blakhall/Kicad/3dmodels/power_dcdc/SY8088AAC.step

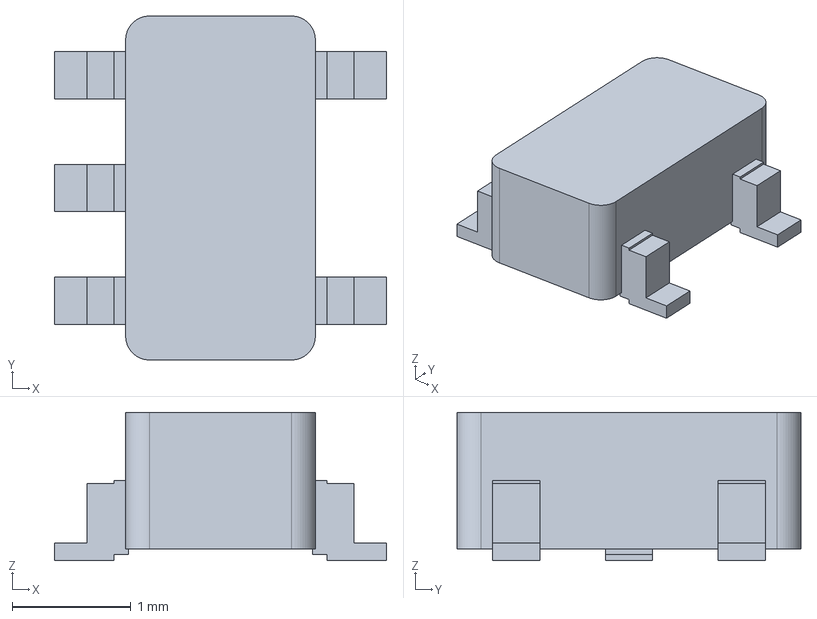
[picture p15: CAD file, 2026-08-23]
3dmodels/power_dcdc/SY8088AAC.step
2.80 x 2.90 x 1.25 mm
