blakhall/Kicad/3dmodels/so_gen/SOIC-6-Stretched_DWY_TI.step

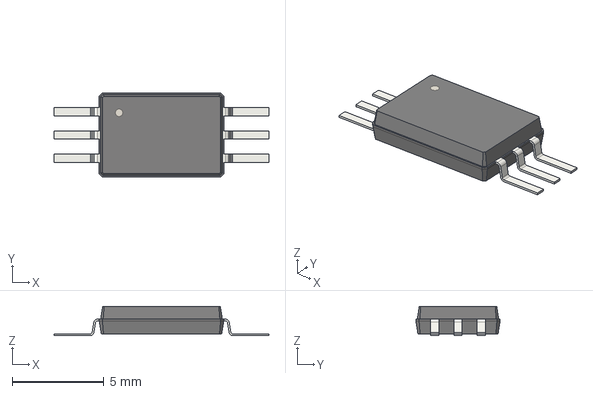
[picture p16: CAD file, 2026-08-02]
3dmodels/so_gen/SOIC-6-Stretched_DWY_TI.step
11.7 x 4.60 x 1.60 mm
