blakhall/Kicad/3dmodels/wpt_driver/SOIC-16_3.9x9.9mm_P1.27mm.step

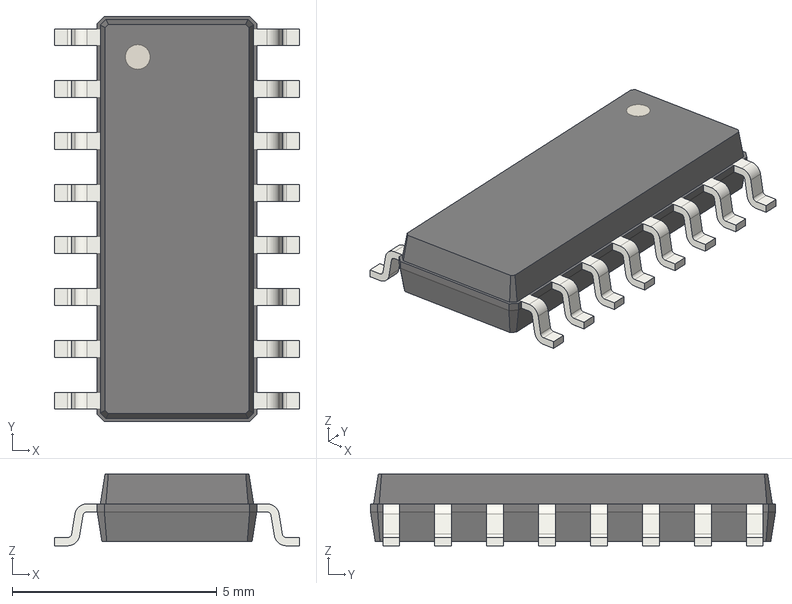
[picture p17: CAD file, 2026-09-19]
3dmodels/wpt_driver/SOIC-16_3.9x9.9mm_P1.27mm.step
6.00 x 9.90 x 1.75 mm
