blakhall/Kicad/3dmodels/wpt_magnetics/SCF29XV-200-2R0A011JV.step

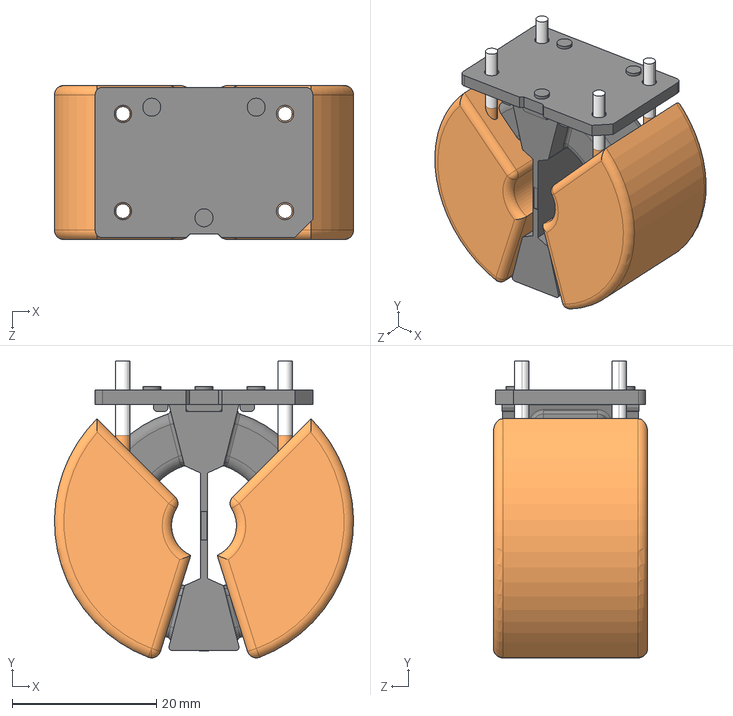
[picture p18: CAD file, 2026-09-19]
3dmodels/wpt_magnetics/SCF29XV-200-2R0A011JV.step
41.5 x 41.2 x 21.4 mm
