blakhall/Kicad/3dmodels/common/Celem_CSM_Nano.step

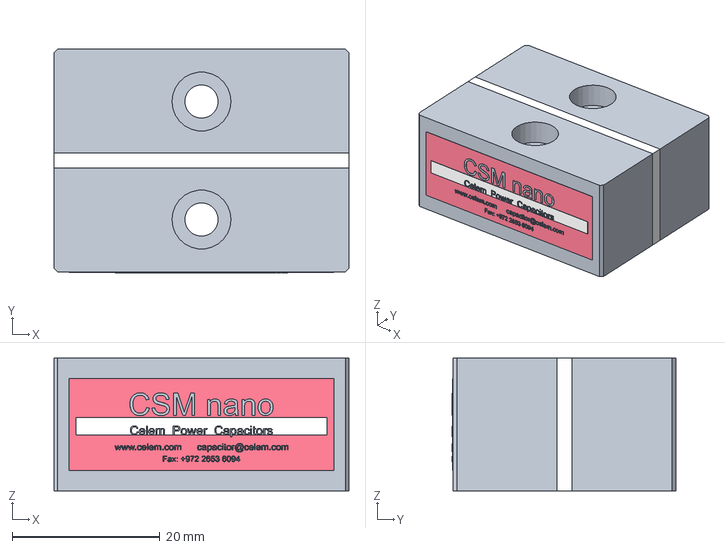
[picture p20: CAD file, 2026-09-17]
3dmodels/common/Celem_CSM_Nano.step
40.0 x 30.3 x 18.0 mm
