blakhall/Kicad/3dmodels/common/led/led-2012-orange.step

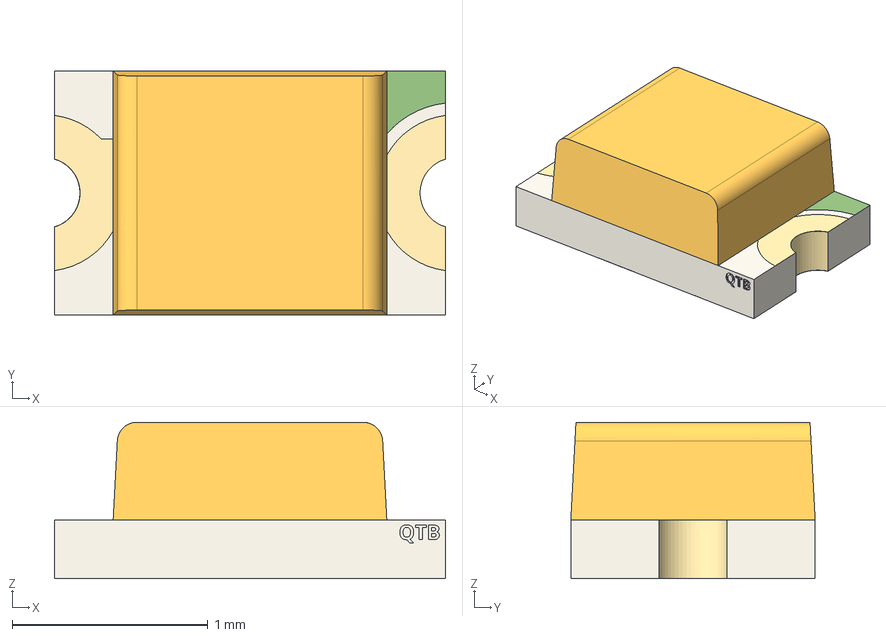
[picture p21: CAD file, 2025-10-02]
3dmodels/common/led/led-2012-orange.step
2.00 x 1.25 x 0.8 mm
Resin
Polarity Mark
Side Pad 1
Side Pad 2
Bottom Pad 2
Top Pad 2
Top Pad 1
Bottom Pad 1
Substrate
Bottom Pad - Mid
