blakhall/Kicad/3dmodels/common_gen/HVSON08_3X3_NXP.step

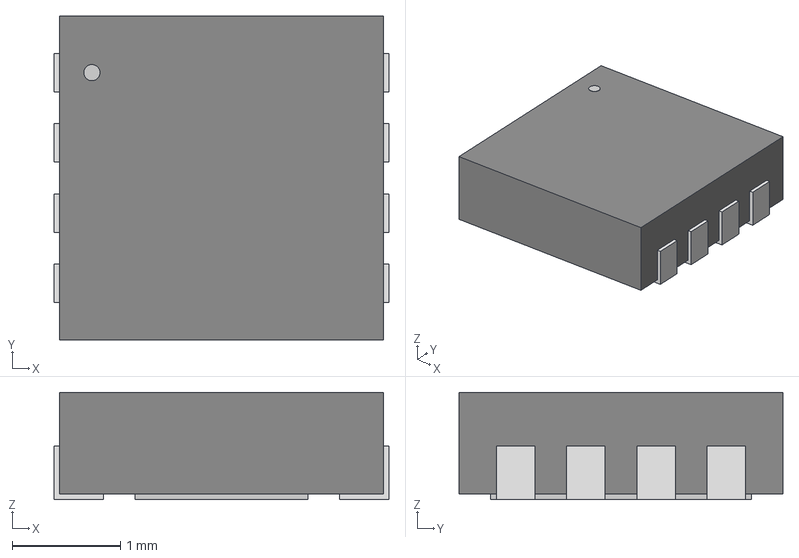
[picture p22: CAD file, 2026-08-17]
3dmodels/common_gen/HVSON08_3X3_NXP.step
3.10 x 3.00 x 0.993 mm
