blakhall/Kicad/3dmodels/connectors/FTR-110-51-L-D-06.step

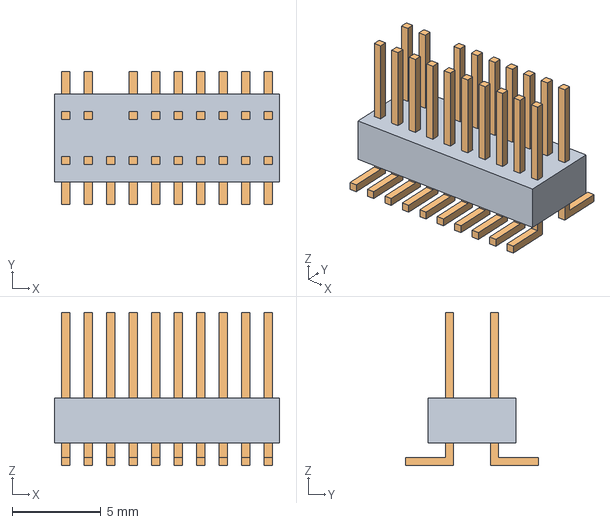
[picture p23: CAD file, 2026-09-19]
3dmodels/connectors/FTR-110-51-L-D-06.step
12.7 x 7.52 x 8.64 mm
