blakhall/Kicad/3dmodels/connectors/optic/HFBR-X41X.STEP

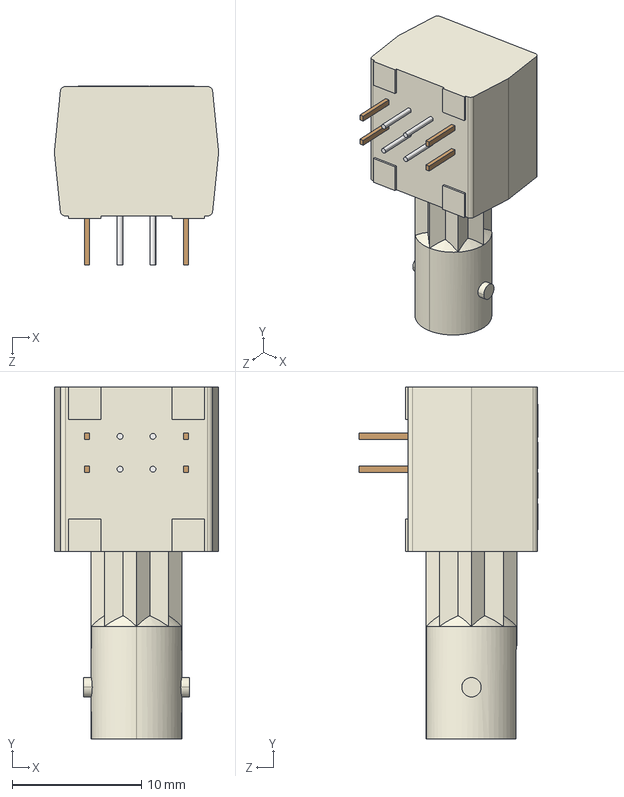
[picture p24: CAD file, 2025-12-01]
3dmodels/connectors/optic/HFBR-X41X.STEP
12.7 x 27.2 x 13.8 mm
HFBR-X41X Part1
HFBR-X41X Part2 x 4
HFBR-X41X Part3 x 4
HFBR-X41X Part4
