blakhall/Kicad/3dmodels/dsp_connectors/FTSH-122-03-L-DV.step

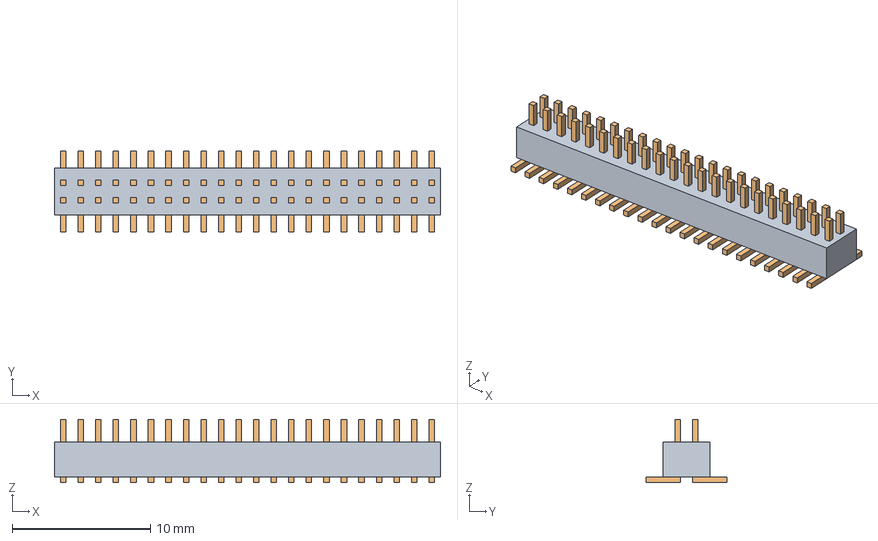
[picture p25: CAD file, 2026-09-19]
3dmodels/dsp_connectors/FTSH-122-03-L-DV.step
27.9 x 5.84 x 4.57 mm
