blakhall/Kicad/3dmodels/mcu_gen/IC_IS31CG5317-LQLS3_LQFP80.step

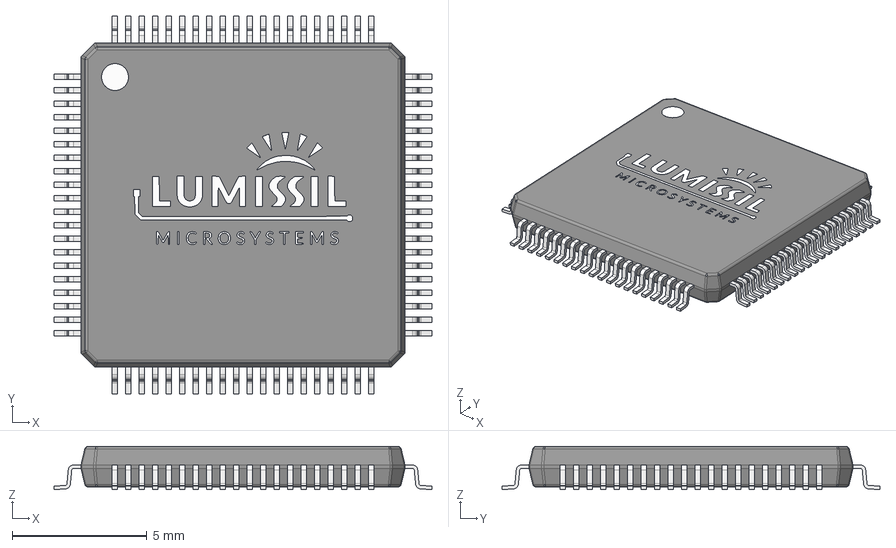
[picture p26: CAD file, 2026-07-20]
3dmodels/mcu_gen/IC_IS31CG5317-LQLS3_LQFP80.step
14.0 x 14.0 x 1.60 mm
Package
Leads
Mark
Logo
