blakhall/Kicad/3dmodels/power_gen/Celem_CSM_IPT.step

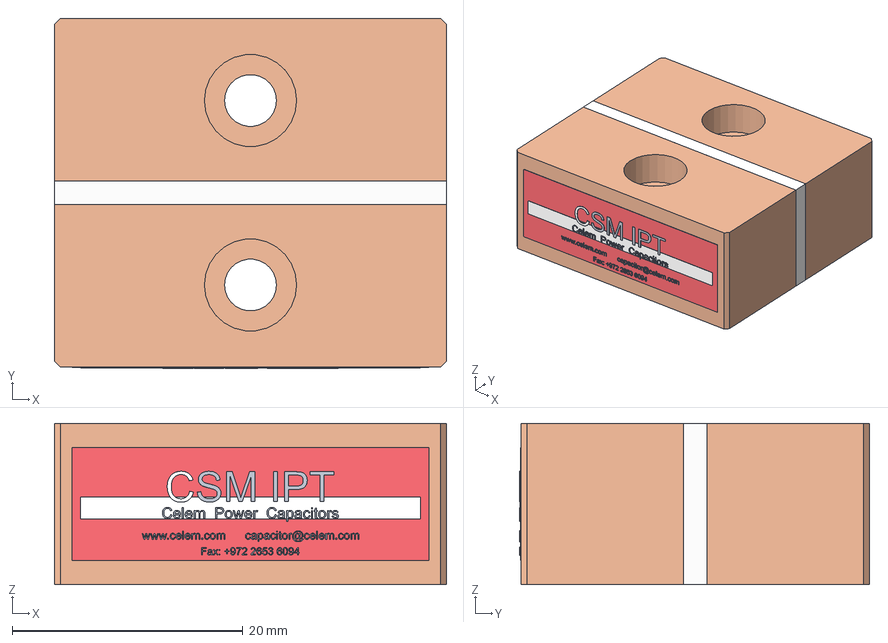
[picture p27: CAD file, 2026-09-17]
3dmodels/power_gen/Celem_CSM_IPT.step
34.0 x 30.3 x 14.0 mm
Copper_Electrode_Front
Copper_Electrode_Rear
Dielectric_Insulator
Celem_Red_Badge
Badge_White_Banner
Badge_Text_Markings
