blakhall/Kicad/3dmodels/so_gen/FC-BPGA-306_SOT2200-1_NXP.step

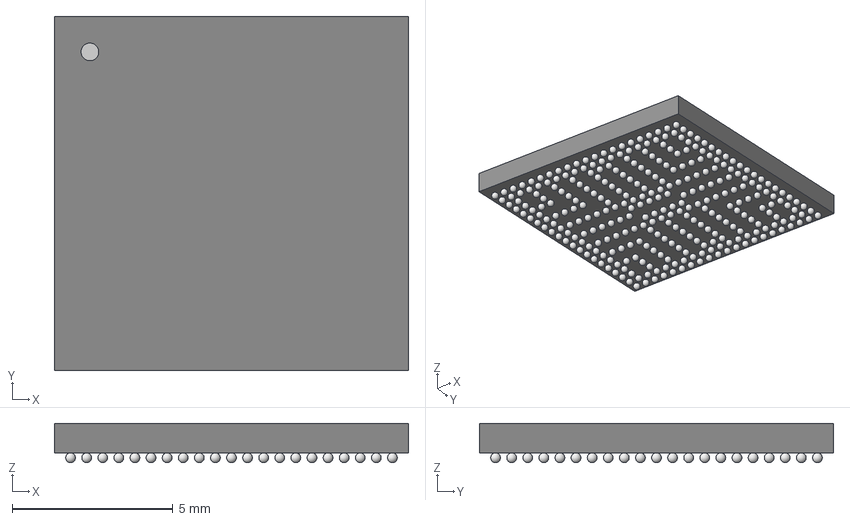
[picture p28: CAD file, 2026-03-11]
3dmodels/so_gen/FC-BPGA-306_SOT2200-1_NXP.step
11.0 x 11.0 x 1.22 mm
