blakhall/Kicad/3dmodels/wpt_driver/VSSOP-8_2.3x2mm_P0.5mm.step

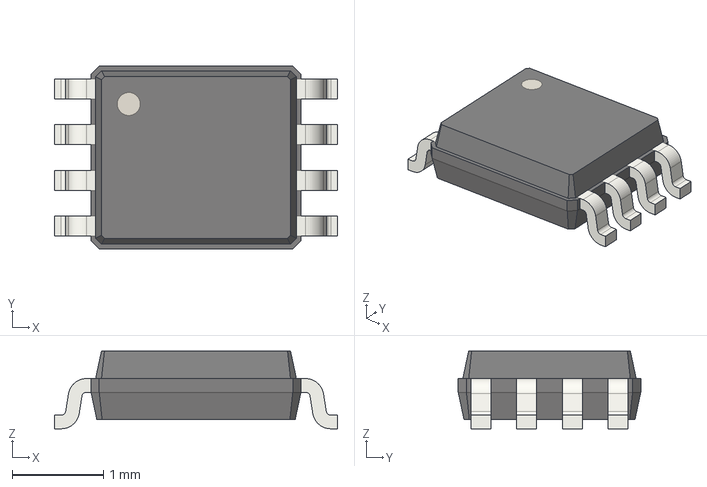
[picture p29: CAD file, 2026-09-19]
3dmodels/wpt_driver/VSSOP-8_2.3x2mm_P0.5mm.step
3.10 x 2.00 x 0.85 mm
