blakhall/Kicad/3dmodels/wpt_sensing/R_1206_3216Metric.step

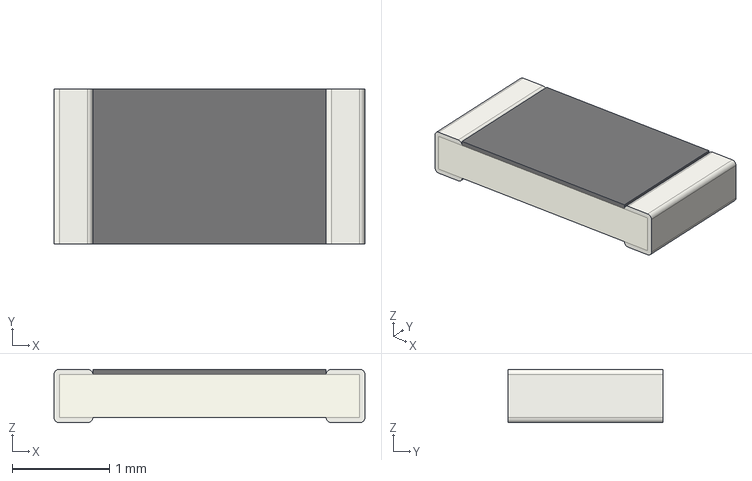
[picture p30: CAD file, 2026-09-19]
3dmodels/wpt_sensing/R_1206_3216Metric.step
3.20 x 1.60 x 0.55 mm
