blakhall/Kicad/3dmodels/common_gen/uQFN-6L_1.5x1.7mm_P0.5mm.step

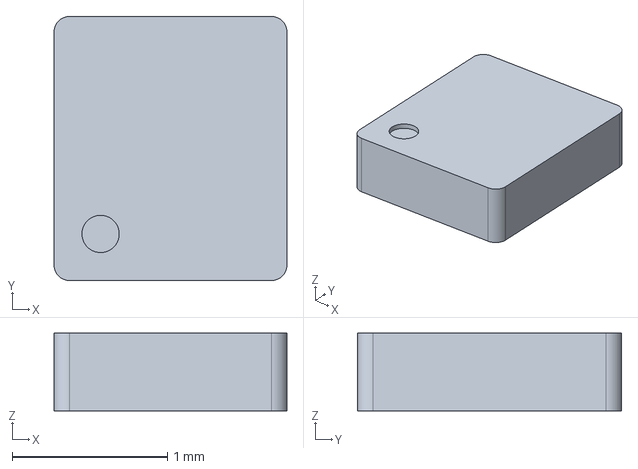
[picture p31: CAD file, 2026-08-17]
3dmodels/common_gen/uQFN-6L_1.5x1.7mm_P0.5mm.step
1.50 x 1.70 x 0.5 mm
