blakhall/Kicad/3dmodels/connectors/FTSH-104-03-L-DV.step

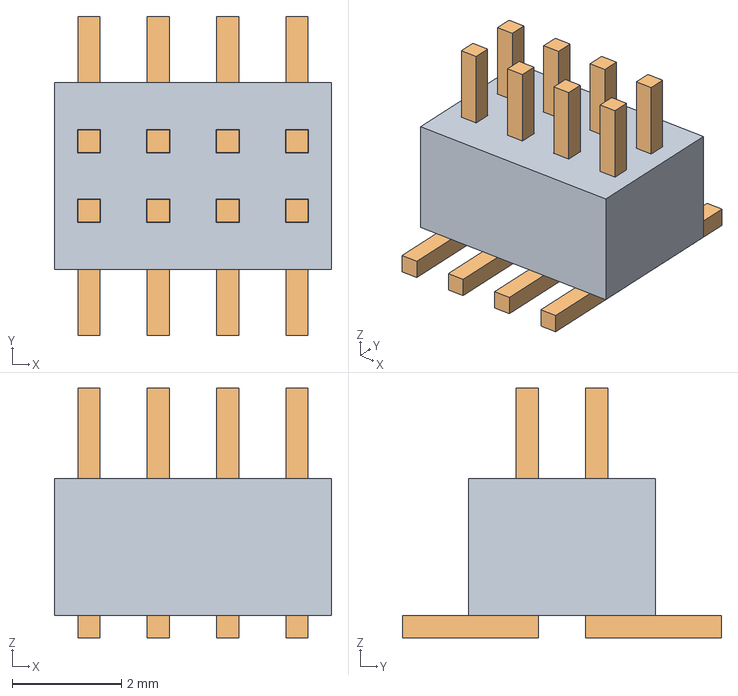
[picture p32: CAD file, 2026-09-19]
3dmodels/connectors/FTSH-104-03-L-DV.step
5.08 x 5.84 x 4.57 mm
