blakhall/Kicad/3dmodels/power_dcdc/SOIC-36W_7.5x12.8mm_P0.65mm_DWN_TI.step

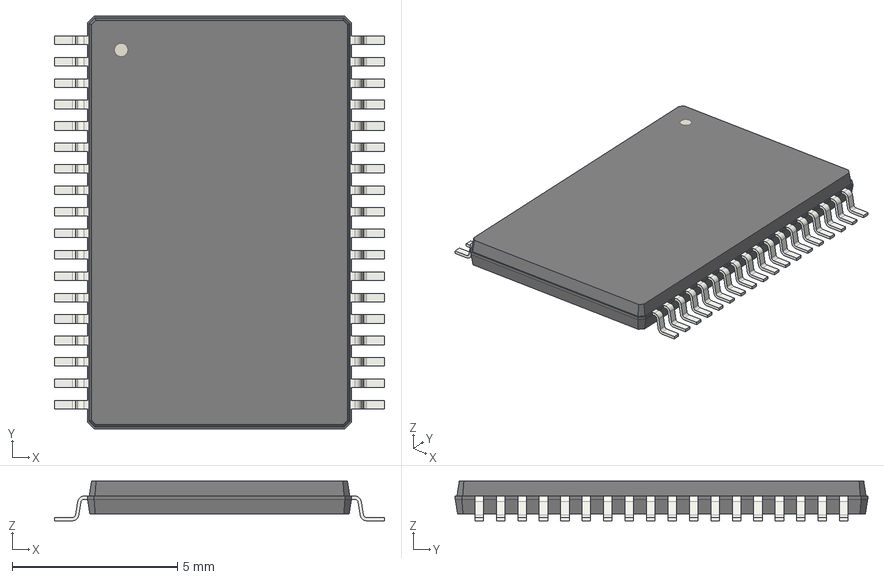
[picture p33: CAD file, 2026-08-02]
3dmodels/power_dcdc/SOIC-36W_7.5x12.8mm_P0.65mm_DWN_TI.step
10.0 x 12.5 x 1.20 mm
