blakhall/Kicad/3dmodels/so_gen/TQFP 128 0.4mm.stp

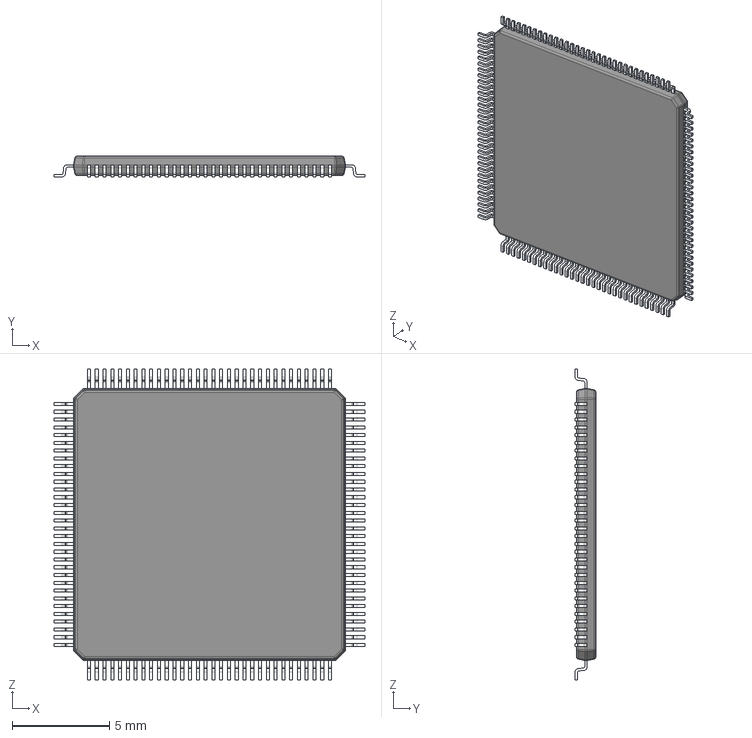
[picture p34: CAD file, 2025-09-22]
3dmodels/so_gen/TQFP 128 0.4mm.stp
16.0 x 1.07 x 16.0 mm
BODY_VJX128A
LEAD_VJX128A x 128
