blakhall/Kicad/3dmodels/wpt_driver/SOT-23-6.step

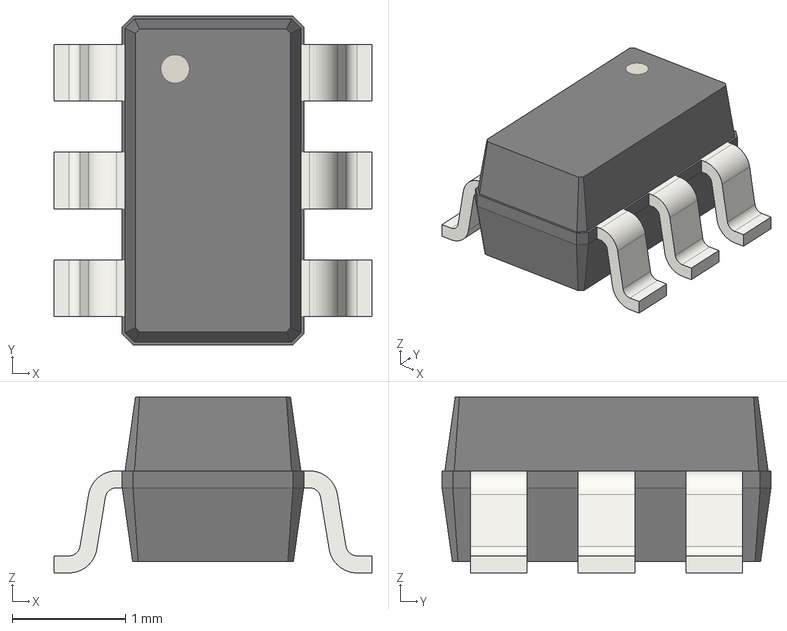
[picture p35: CAD file, 2026-09-19]
3dmodels/wpt_driver/SOT-23-6.step
2.80 x 2.90 x 1.55 mm
