blakhall/Kicad/3dmodels/common/SCF29XV-150-1R7A015JV.step

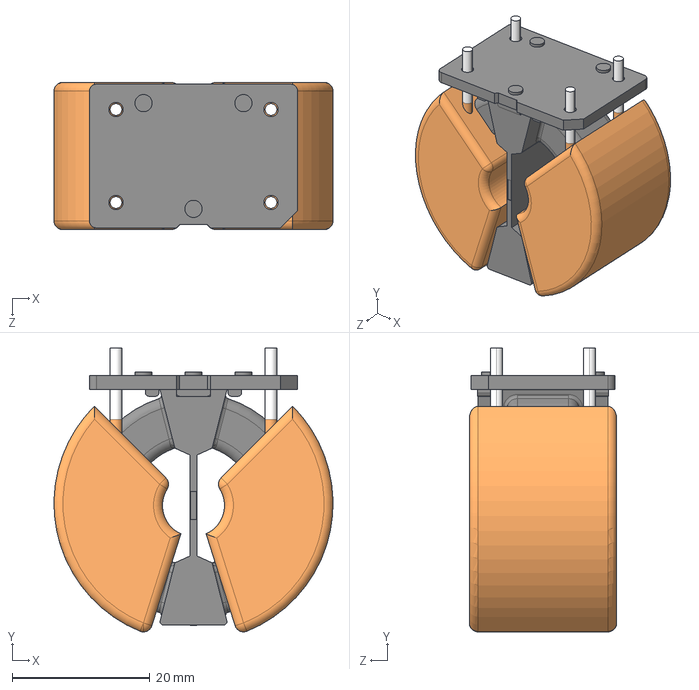
[picture p37: CAD file, 2026-09-09]
3dmodels/common/SCF29XV-150-1R7A015JV.step
40.5 x 41.2 x 21.4 mm
