blakhall/Kicad/3dmodels/connectors/USB4105GFA.step

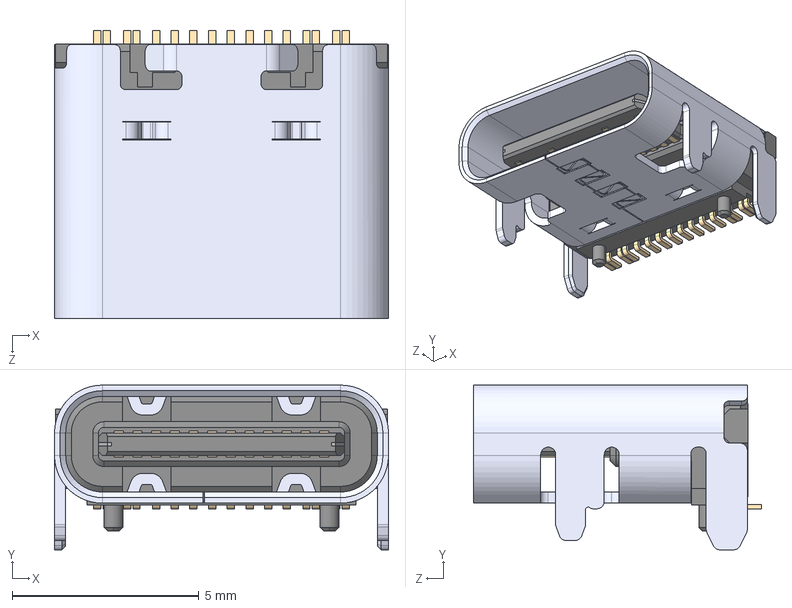
[picture p38: CAD file, 2026-08-17]
3dmodels/connectors/USB4105GFA.step
8.94 x 4.41 x 7.71 mm
