blakhall/Kicad/3dmodels/power_dcdc/Converter_DCDC_MeanWell_SKMW20G-12.step

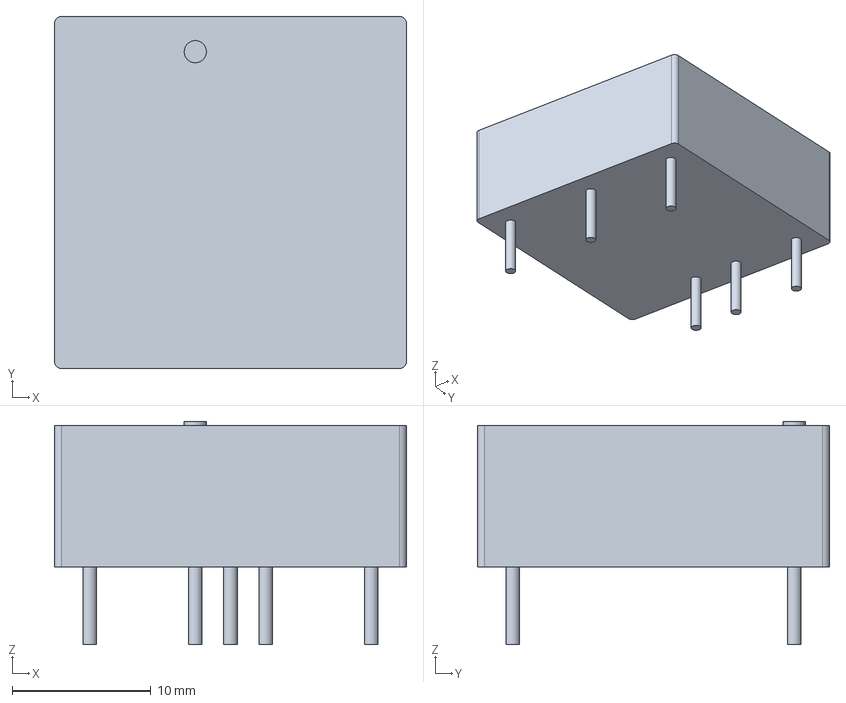
[picture p39: CAD file, 2026-08-02]
3dmodels/power_dcdc/Converter_DCDC_MeanWell_SKMW20G-12.step
25.4 x 25.4 x 16.1 mm
