blakhall/Kicad/3dmodels/power_gen/T9AS5D12-5.step

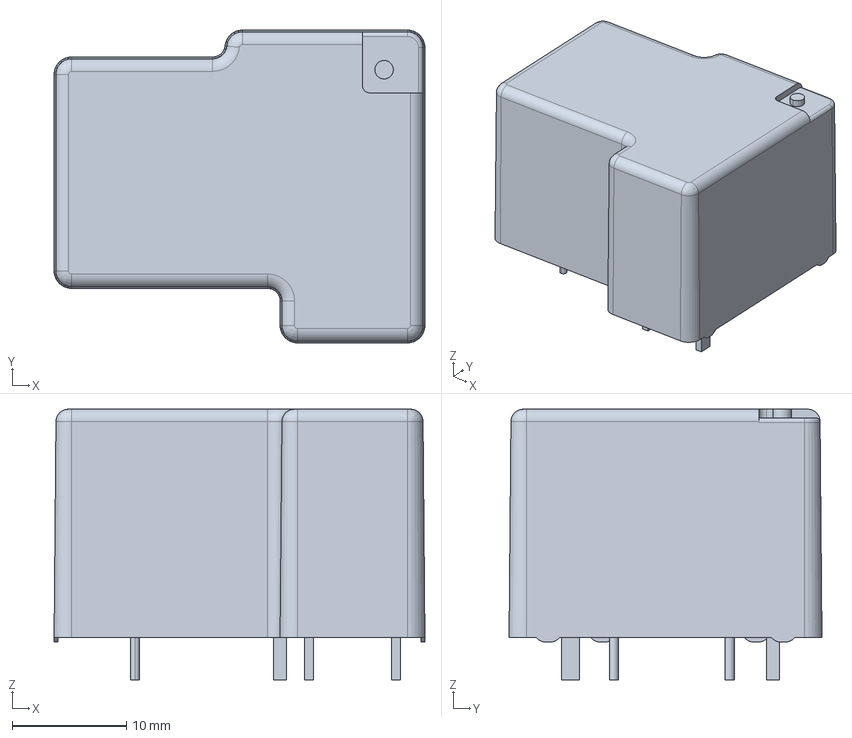
[picture p40: CAD file, 2026-09-08]
3dmodels/power_gen/T9AS5D12-5.step
32.5 x 27.4 x 23.7 mm
