blakhall/Kicad/3dmodels/wpt_driver/SOIC-8_3.9x4.9mm_P1.27mm.step

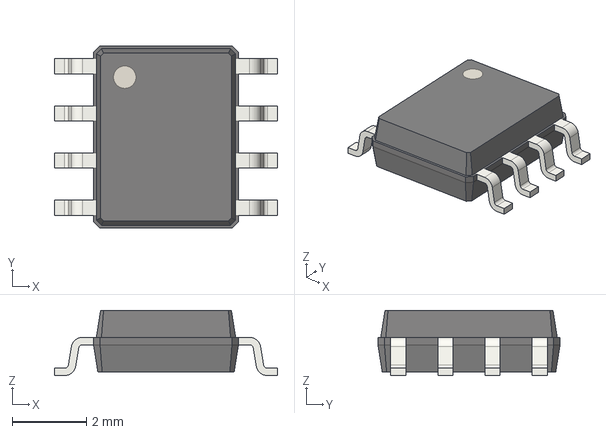
[picture p41: CAD file, 2026-09-19]
3dmodels/wpt_driver/SOIC-8_3.9x4.9mm_P1.27mm.step
6.00 x 4.90 x 1.75 mm
