blakhall/Kicad/3dmodels/wpt_sensing/SOIC-16W_7.5x10.3mm_P1.27mm.step

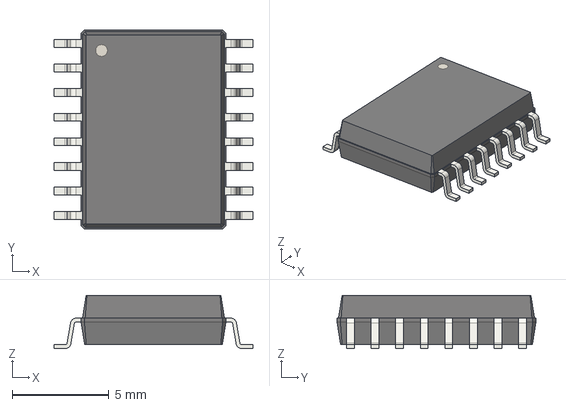
[picture p42: CAD file, 2026-09-19]
3dmodels/wpt_sensing/SOIC-16W_7.5x10.3mm_P1.27mm.step
10.3 x 10.3 x 2.75 mm
