blakhall/Kicad/3dmodels/common/Filter_DataLine_Coilcraft_PDLF_8SMD.step

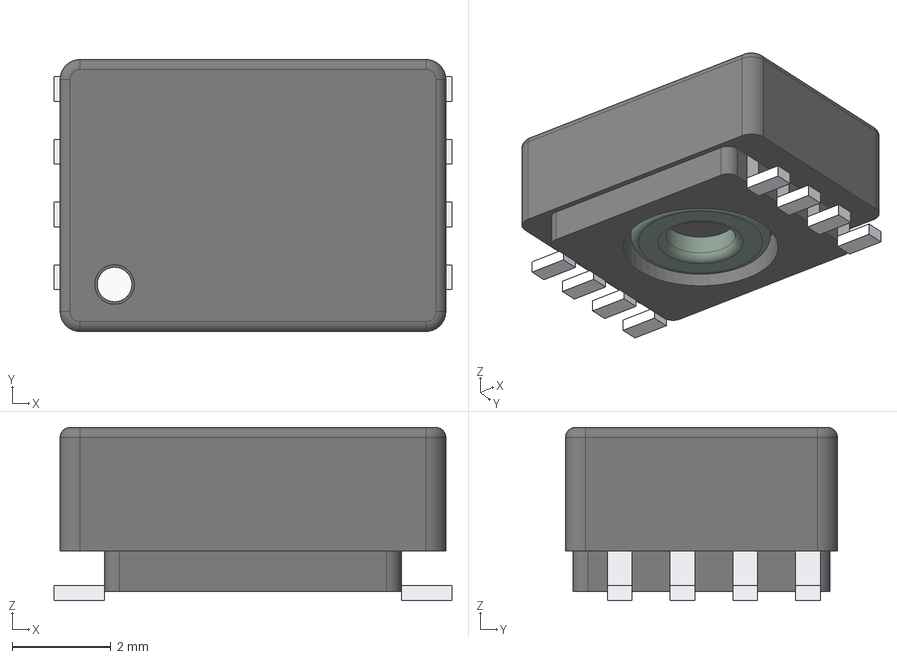
[picture p43: CAD file, 2026-09-09]
3dmodels/common/Filter_DataLine_Coilcraft_PDLF_8SMD.step
8.05 x 5.50 x 3.50 mm
Pin1Dot
Leads
Toroid
