blakhall/Kicad/3dmodels/connectors/CLP-104-02-F-D-TR.stp

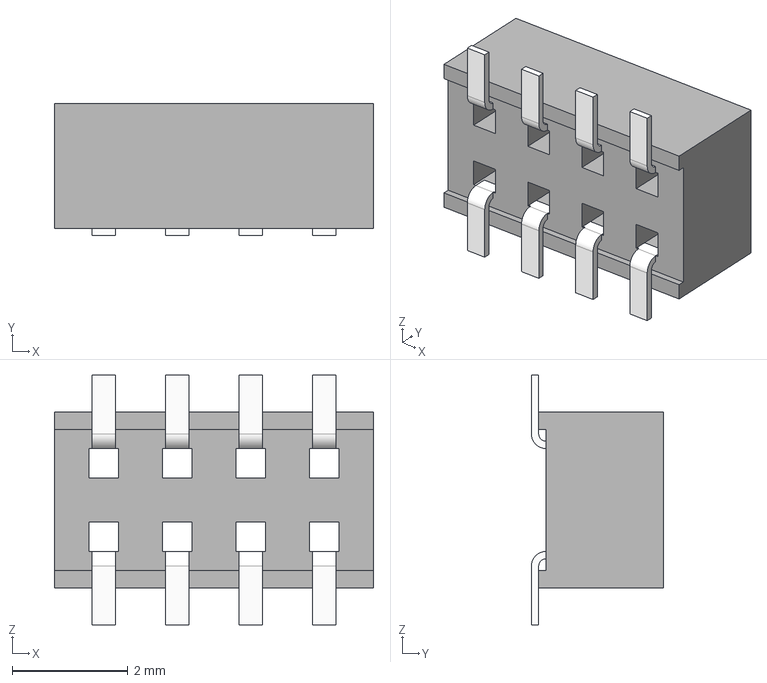
[picture p44: CAD file, 2026-08-17]
3dmodels/connectors/CLP-104-02-F-D-TR.stp
5.51 x 2.29 x 4.32 mm
CLP-104-2-F-D-TRTRM
C-106-22-1-F-04_Pin x 2
