blakhall/Kicad/3dmodels/power_dcdc/Converter_DCDC_TRACO_THN-20UIR.step

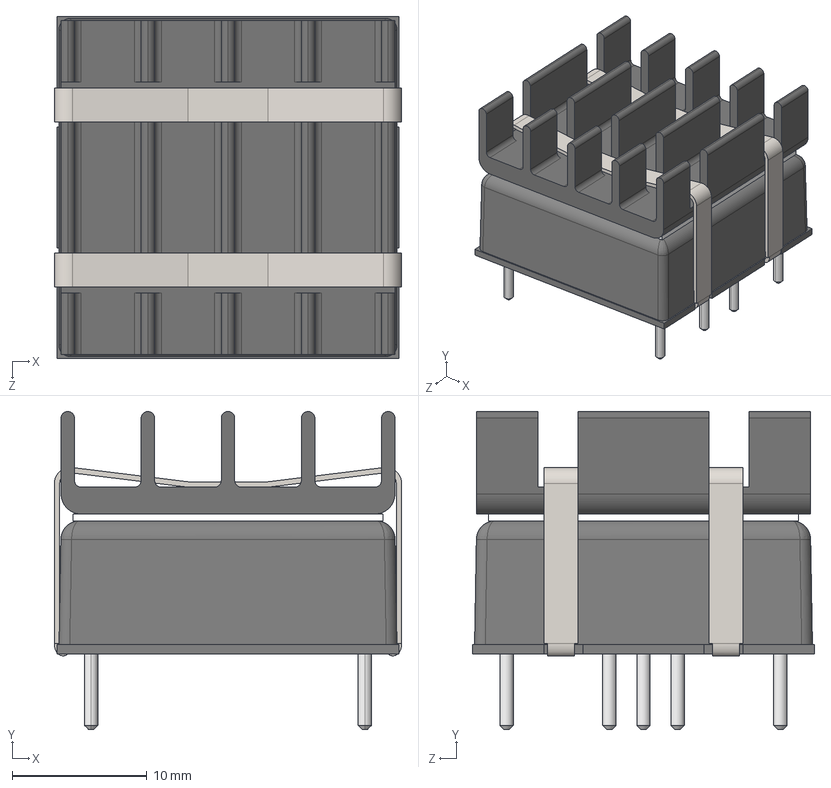
[picture p45: CAD file, 2026-08-02]
3dmodels/power_dcdc/Converter_DCDC_TRACO_THN-20UIR.step
25.8 x 23.6 x 25.4 mm
