blakhall/Kicad/3dmodels/power_gen/AIF04ZPFC-01NTL.step

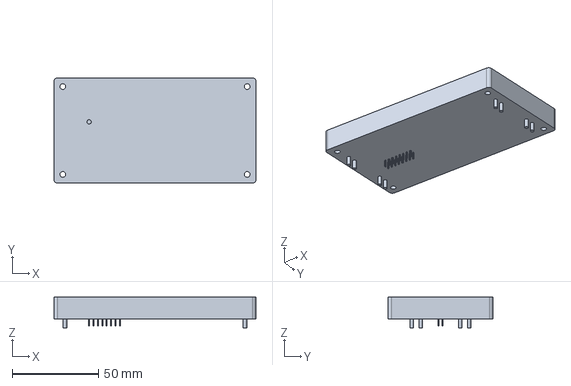
[picture p46: CAD file, 2026-09-08]
3dmodels/power_gen/AIF04ZPFC-01NTL.step
116.8 x 61.0 x 17.7 mm
