blakhall/Kicad/3dmodels/so_gen/FBGA13x13x0.65mm.stp

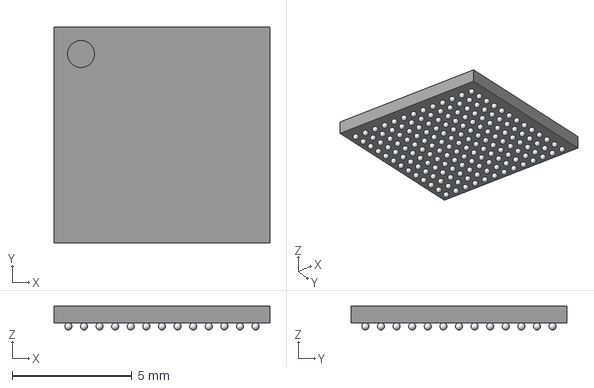
[picture p47: CAD file, 2025-09-21]
3dmodels/so_gen/FBGA13x13x0.65mm.stp
9.00 x 9.00 x 1.00 mm
