blakhall/Kicad/3dmodels/common/Converter_DCDC_Mornsun_QAxx3C-R3S_THT.step

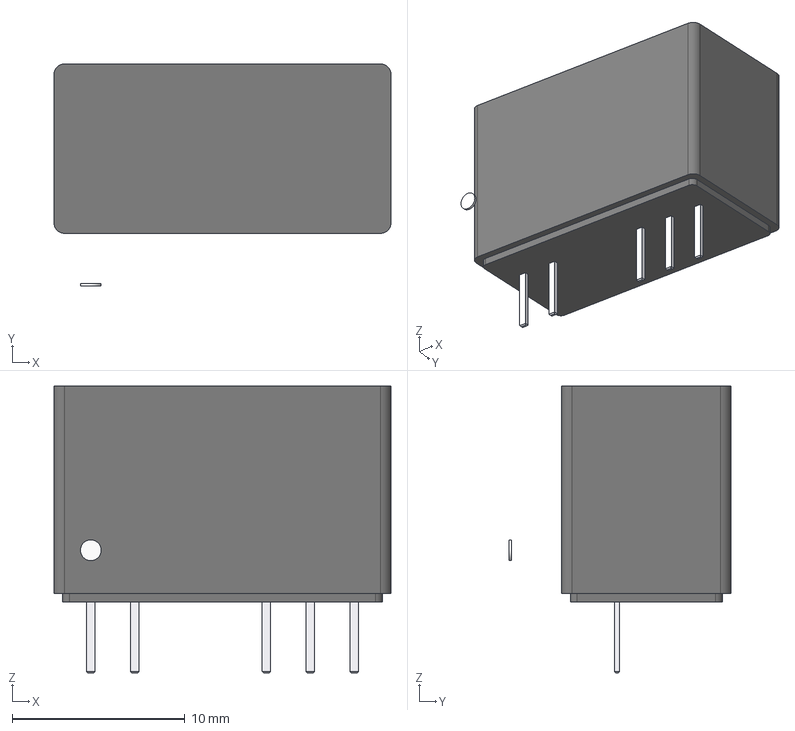
[picture p48: CAD file, 2026-09-09]
3dmodels/common/Converter_DCDC_Mornsun_QAxx3C-R3S_THT.step
19.5 x 12.8 x 16.6 mm
pins
dot
