blakhall/Kicad/3dmodels/power_dcdc/Converter_DCDC_Mornsun_XT-1WR3_SMD.step

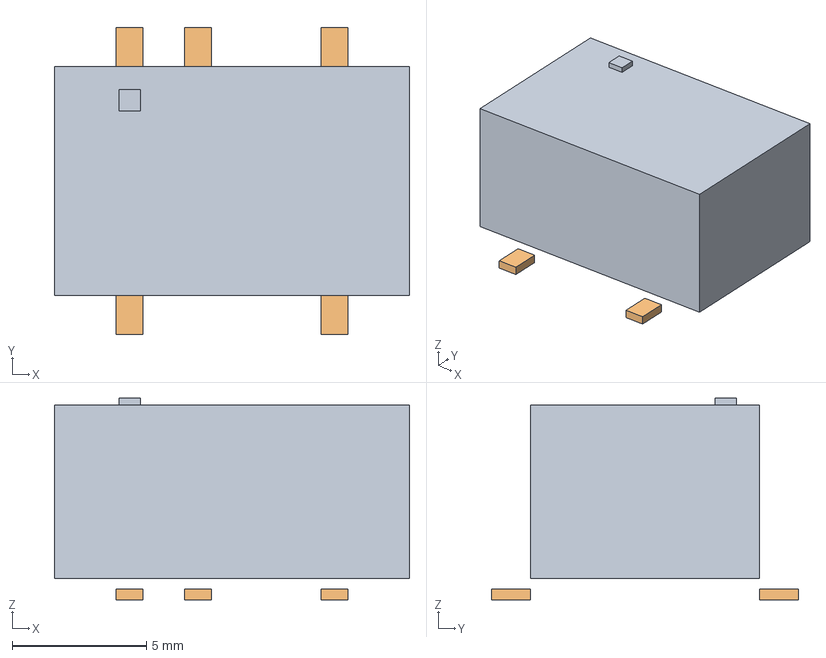
[picture p49: CAD file, 2026-07-20]
3dmodels/power_dcdc/Converter_DCDC_Mornsun_XT-1WR3_SMD.step
13.2 x 11.4 x 7.50 mm
