blakhall/Kicad/3dmodels/power_gen/Texas_RAK0009A_WQFN-HR-9_2.5x2.0mm.step

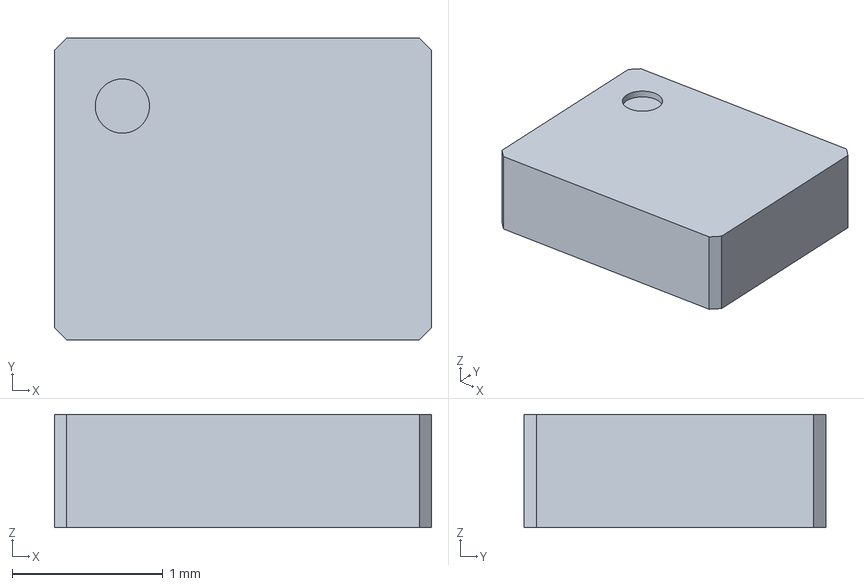
[picture p50: CAD file, 2026-09-04]
3dmodels/power_gen/Texas_RAK0009A_WQFN-HR-9_2.5x2.0mm.step
2.50 x 2.00 x 0.75 mm
