blakhall/Kicad/3dmodels/common/D_DO-216AA.step

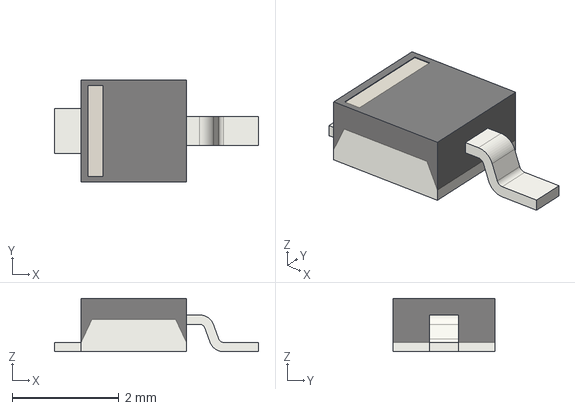
[picture p51: CAD file, 2026-09-09]
3dmodels/common/D_DO-216AA.step
3.82 x 1.90 x 1.00 mm
