blakhall/Kicad/3dmodels/connectors/S3B-PH-K-S.step

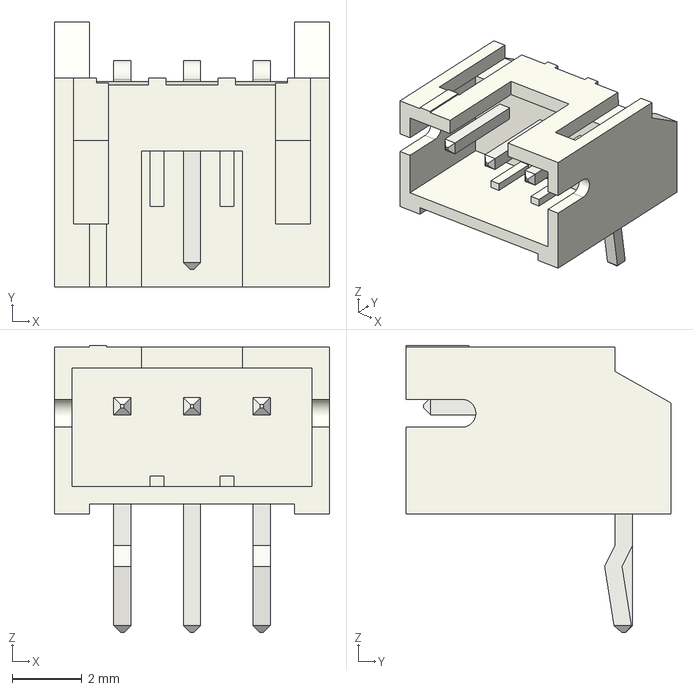
[picture p52: CAD file, 2026-07-23]
3dmodels/connectors/S3B-PH-K-S.step
7.90 x 7.60 x 8.25 mm
