blakhall/Kicad/3dmodels/power_dcdc/Converter_DCDC_RECOM_R1SE_SMD.step

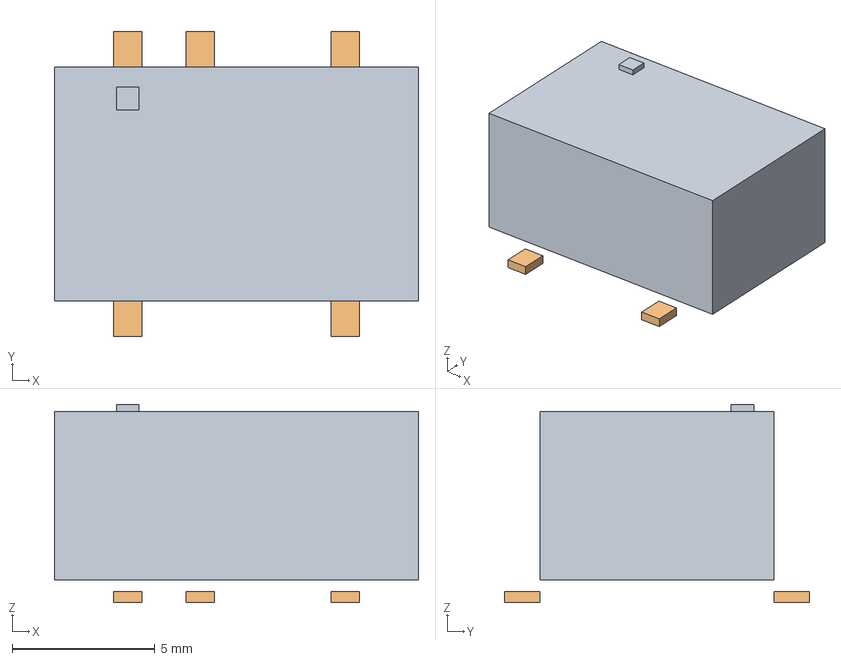
[picture p53: CAD file, 2026-07-20]
3dmodels/power_dcdc/Converter_DCDC_RECOM_R1SE_SMD.step
12.8 x 10.7 x 6.95 mm
