blakhall/Kicad/3dmodels/common/SOIC-14_7.5x10.3mm_P1.27mm_TI_DWK0014A.step

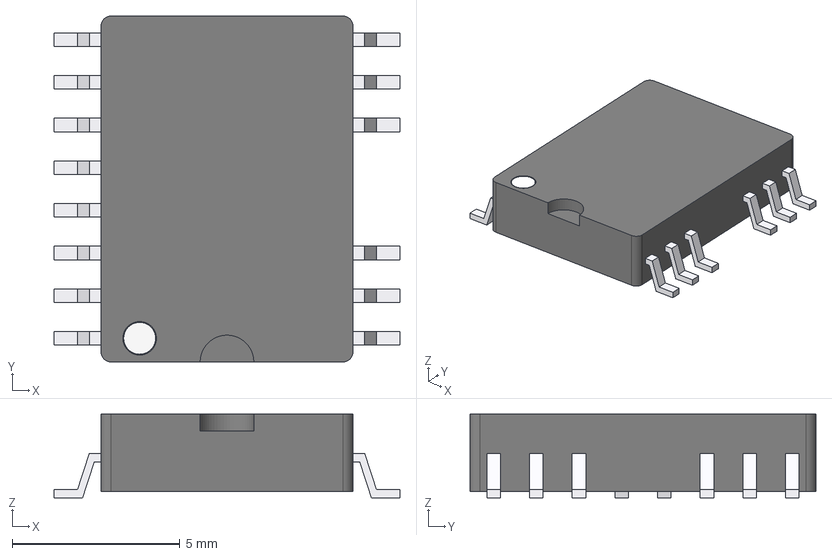
[picture p54: CAD file, 2026-09-09]
3dmodels/common/SOIC-14_7.5x10.3mm_P1.27mm_TI_DWK0014A.step
10.3 x 10.3 x 2.50 mm
Pin1Dot
Leads
