blakhall/Kicad/3dmodels/common_gen/ECMF02-4CMX8.step

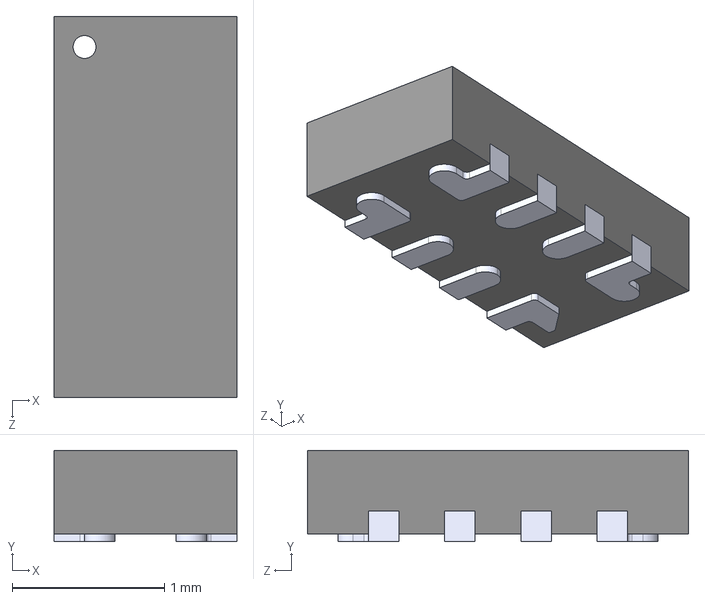
[picture p55: CAD file, 2026-04-05]
3dmodels/common_gen/ECMF02-4CMX8.step
1.20 x 0.6 x 2.50 mm
