blakhall/Kicad/3dmodels/connectors/B4B-PH-K-S.step

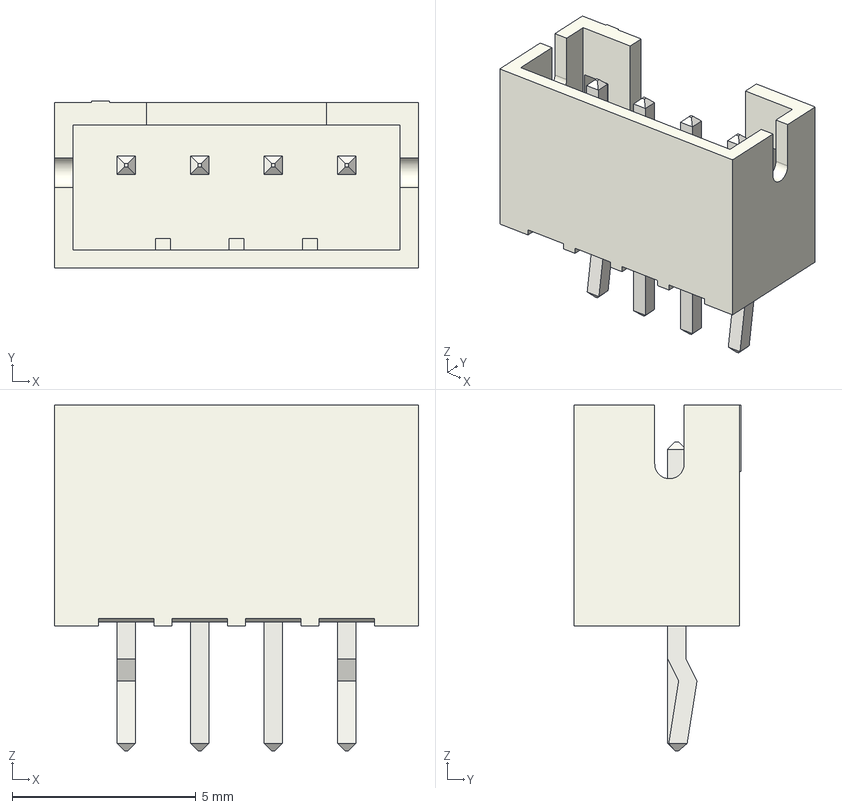
[picture p56: CAD file, 2026-07-23]
3dmodels/connectors/B4B-PH-K-S.step
9.90 x 4.55 x 9.40 mm
