blakhall/Kicad/3dmodels/power_dcdc/MIE1W0505BGLVH-3R-Z.step

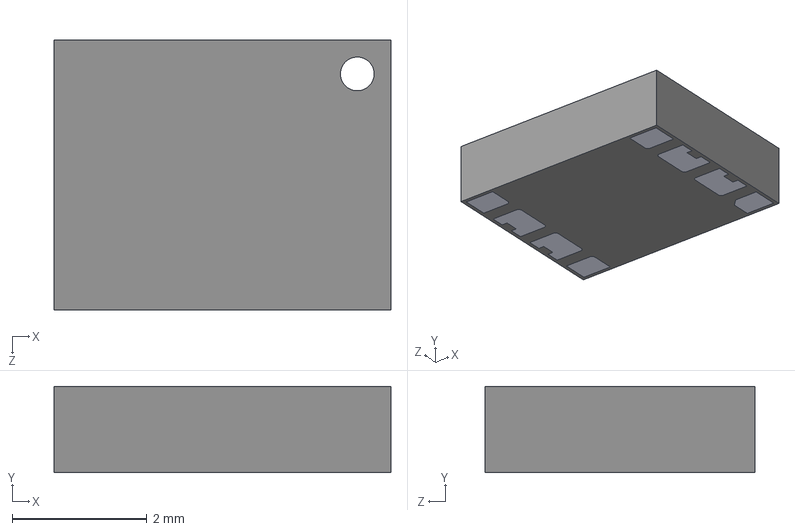
[picture p57: CAD file, 2025-08-17]
3dmodels/power_dcdc/MIE1W0505BGLVH-3R-Z.step
5.00 x 1.28 x 4.00 mm
