blakhall/Kicad/3dmodels/common/Infineon_PG-DSO-14_2EDB8259Y.step

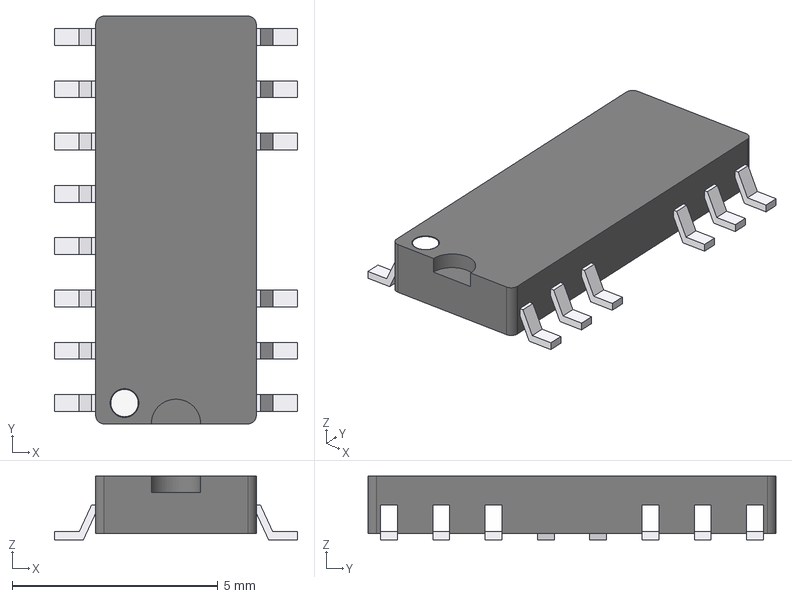
[picture p58: CAD file, 2026-09-09]
3dmodels/common/Infineon_PG-DSO-14_2EDB8259Y.step
5.90 x 9.90 x 1.55 mm
Pin1Dot
Leads
