blakhall/Kicad/3dmodels/connectors/S6B-PH-K-S.step

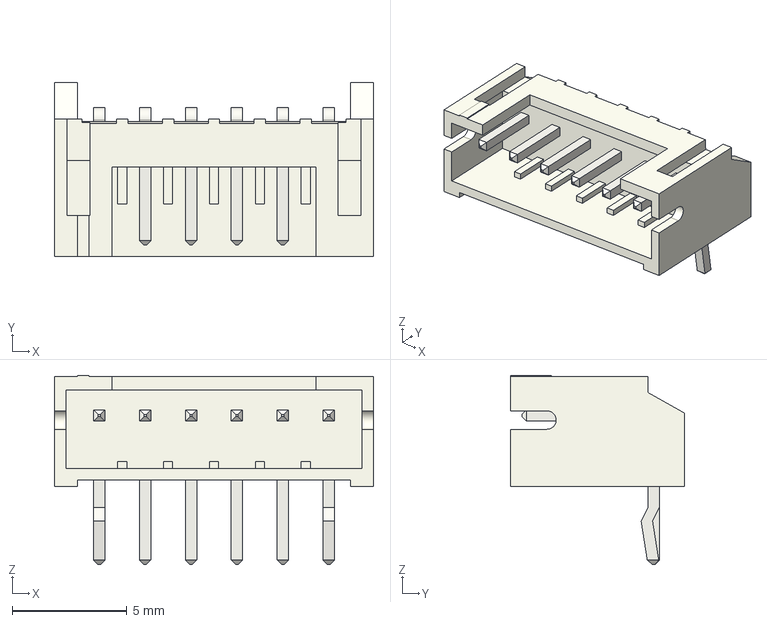
[picture p59: CAD file, 2026-07-23]
3dmodels/connectors/S6B-PH-K-S.step
13.9 x 7.60 x 8.25 mm
