blakhall/Kicad/3dmodels/power_dcdc/mps_dcdc_mev1s_5&12&15&24vin_sc_a.step

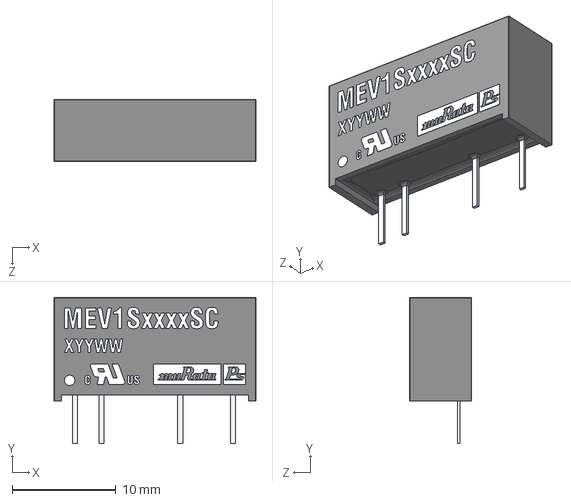
[picture p60: CAD file, 2025-07-06]
3dmodels/power_dcdc/mps_dcdc_mev1s_5&12&15&24vin_sc_a.step
19.5 x 14.1 x 6.02 mm
