blakhall/Kicad/3dmodels/common/Transformer_CurrentSense_Pulse_PAS6322.step

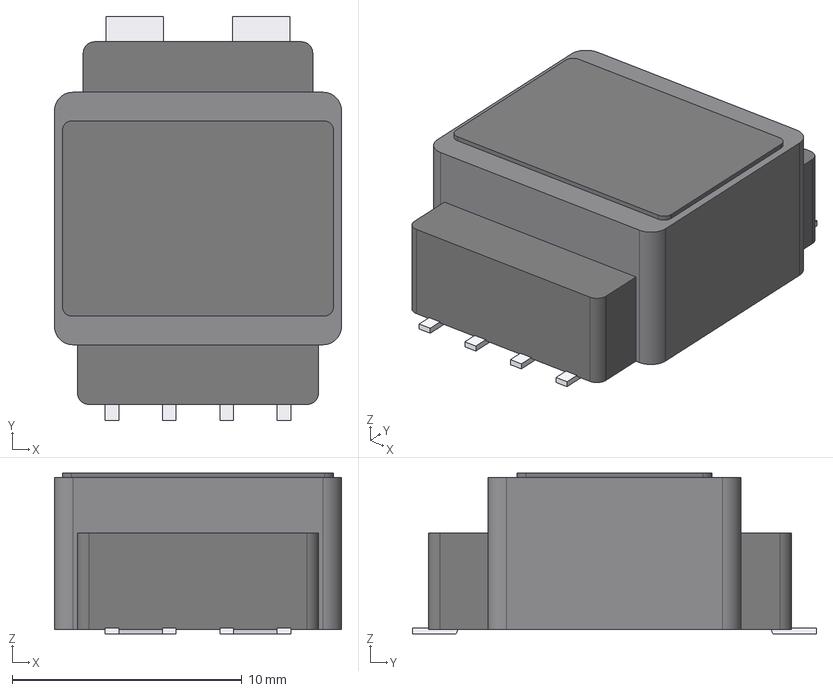
[picture p61: CAD file, 2026-09-08]
3dmodels/common/Transformer_CurrentSense_Pulse_PAS6322.step
12.5 x 17.6 x 7.00 mm
Core
Bobbin
Leads
Pin1Dot
