blakhall/Kicad/3dmodels/connectors/B5B-PH-K-S.step

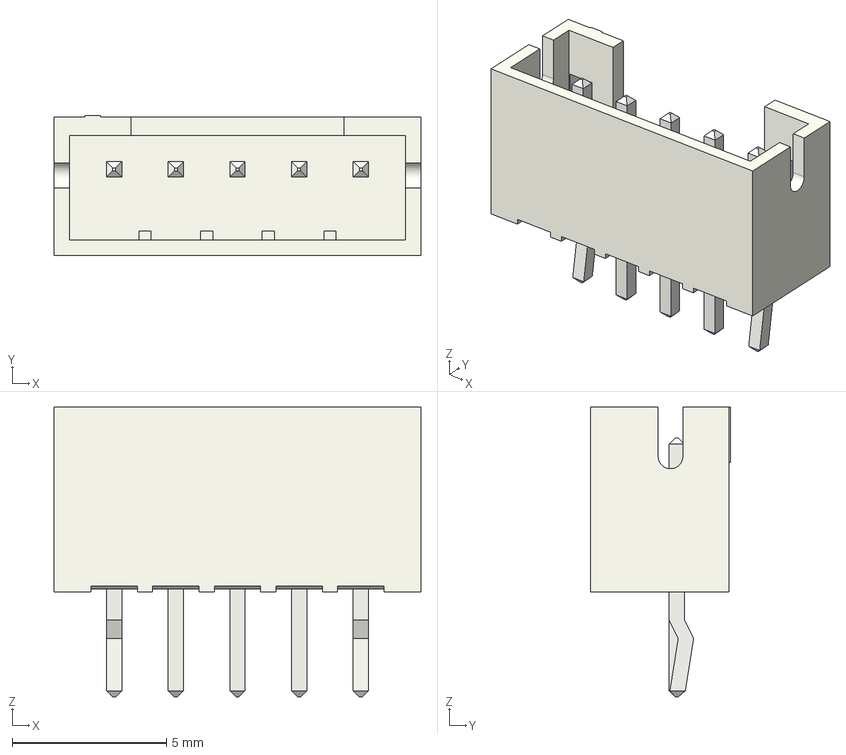
[picture p62: CAD file, 2026-07-23]
3dmodels/connectors/B5B-PH-K-S.step
11.9 x 4.55 x 9.40 mm
