blakhall/Kicad/3dmodels/power_gen/Choke_PFC_ITG_PFC282820B-900MHF.step

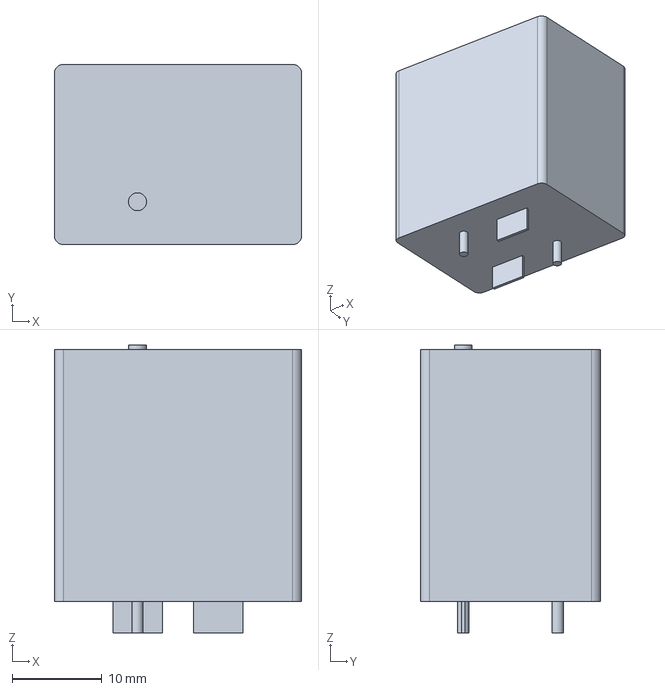
[picture p63: CAD file, 2026-07-23]
3dmodels/power_gen/Choke_PFC_ITG_PFC282820B-900MHF.step
27.5 x 20.0 x 32.0 mm
