blakhall/Kicad/3dmodels/common/CD-HD2004L.step

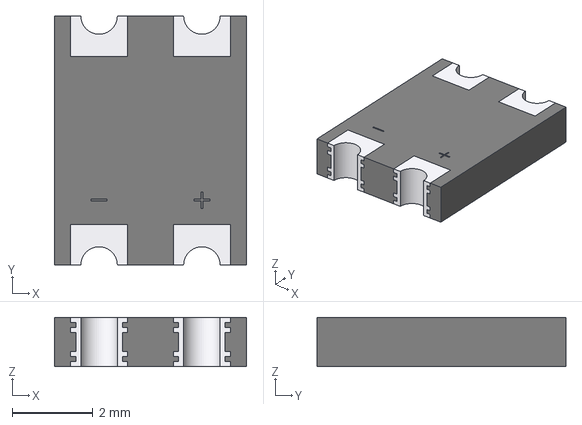
[picture p64: CAD file, 2026-09-08]
3dmodels/common/CD-HD2004L.step
4.75 x 6.15 x 1.22 mm
Leads
