blakhall/Kicad/3dmodels/connectors/B2B-PH-K-S.step

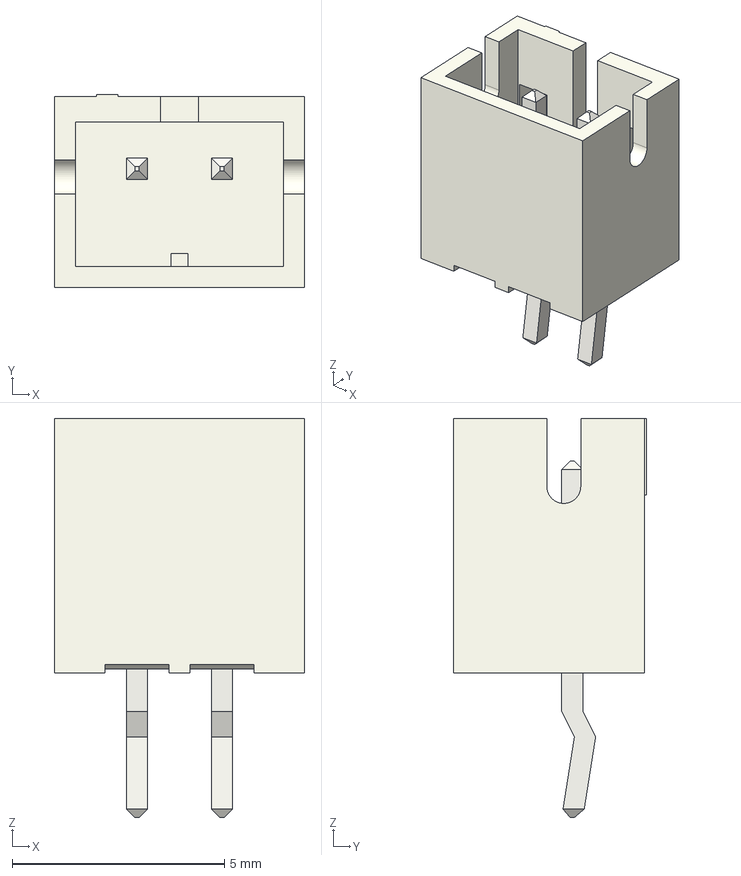
[picture p65: CAD file, 2026-07-23]
3dmodels/connectors/B2B-PH-K-S.step
5.90 x 4.55 x 9.40 mm
