blakhall/Kicad/3dmodels/common/Keystone_8174.step

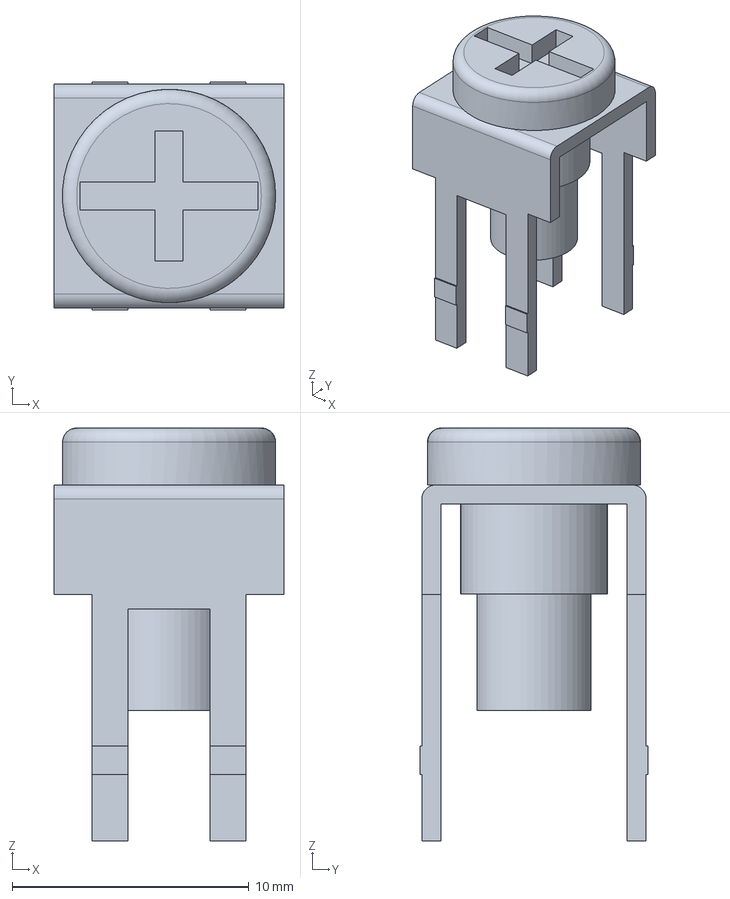
[picture p66: CAD file, 2026-09-08]
3dmodels/common/Keystone_8174.step
9.70 x 9.63 x 17.4 mm
