blakhall/Kicad/3dmodels/connectors/S2B-PH-K-S.step

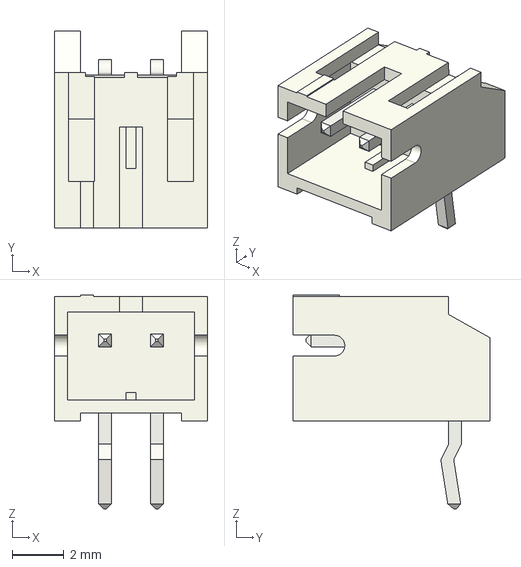
[picture p67: CAD file, 2026-07-23]
3dmodels/connectors/S2B-PH-K-S.step
5.90 x 7.60 x 8.25 mm
