blakhall/Kicad/3dmodels/power_gen/IPTC007N06NM5ATMA1.stp

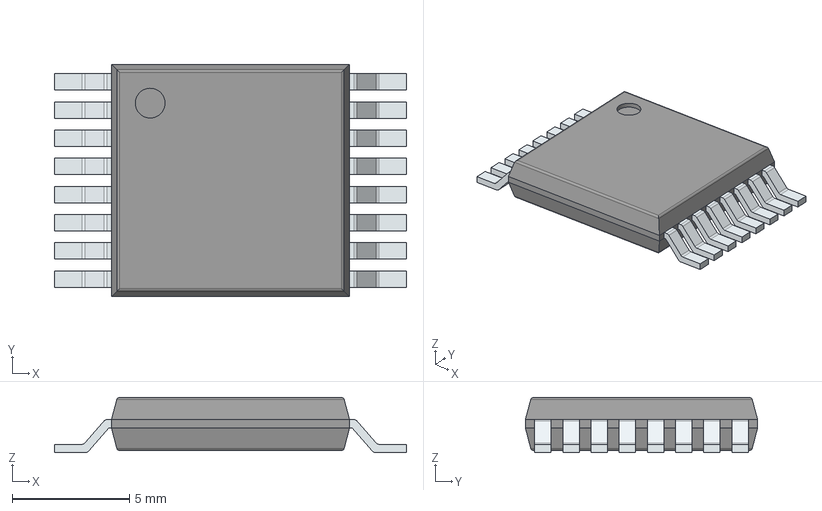
[picture p68: CAD file, 2025-09-21]
3dmodels/power_gen/IPTC007N06NM5ATMA1.stp
15.0 x 9.90 x 2.35 mm
PinsArrayLR
