blakhall/Kicad/3dmodels/common/R76PR368050H4J.step

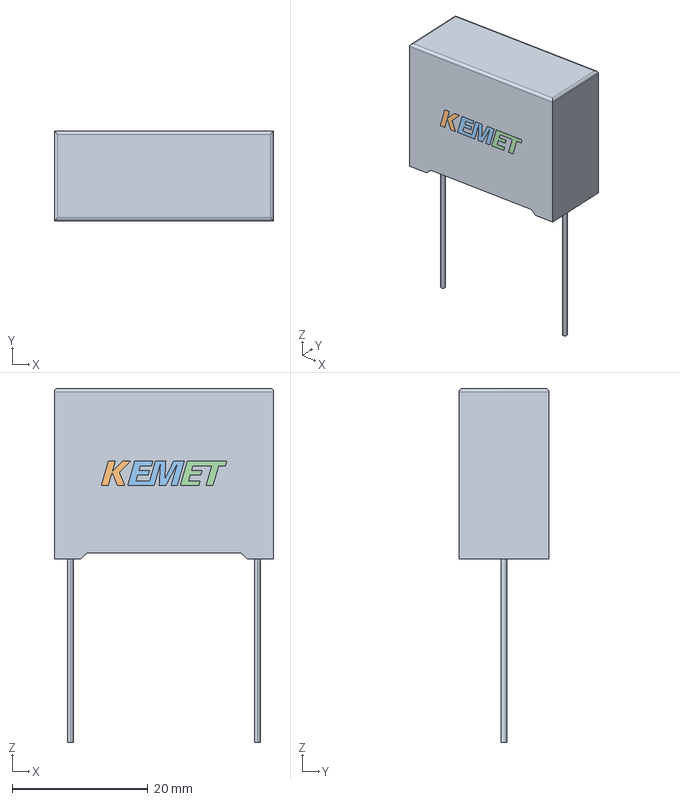
[picture p69: CAD file, 2026-09-08]
3dmodels/common/R76PR368050H4J.step
32.3 x 13.2 x 52.1 mm
