blakhall/Kicad/3dmodels/connectors/S5B-PH-K-S.step

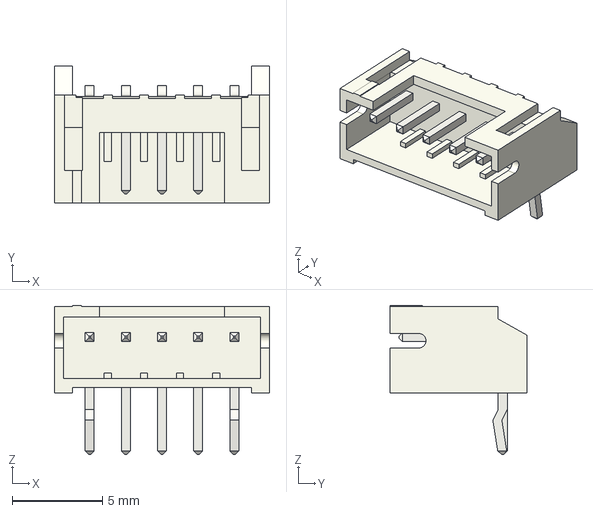
[picture p70: CAD file, 2026-07-23]
3dmodels/connectors/S5B-PH-K-S.step
11.9 x 7.60 x 8.25 mm
