blakhall/Kicad/3dmodels/power_gen/infineon-pg-hdsop-16-8-3d-12-stp-package-en.stp

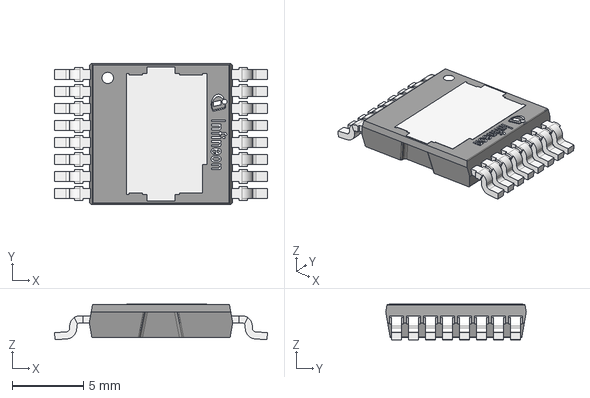
[picture p71: CAD file, 2025-09-21]
3dmodels/power_gen/infineon-pg-hdsop-16-8-3d-12-stp-package-en.stp
15.0 x 9.90 x 2.50 mm
