blakhall/Kicad/3dmodels/common/SC-30-D010.step

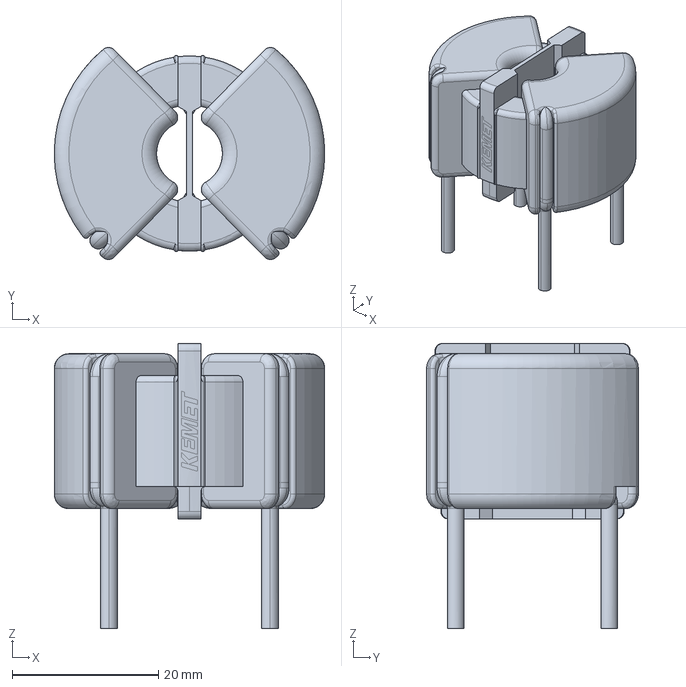
[picture p72: CAD file, 2026-09-08]
3dmodels/common/SC-30-D010.step
37.0 x 29.0 x 39.0 mm
