blakhall/Kicad/3dmodels/connectors/B6B-PH-K-S.step

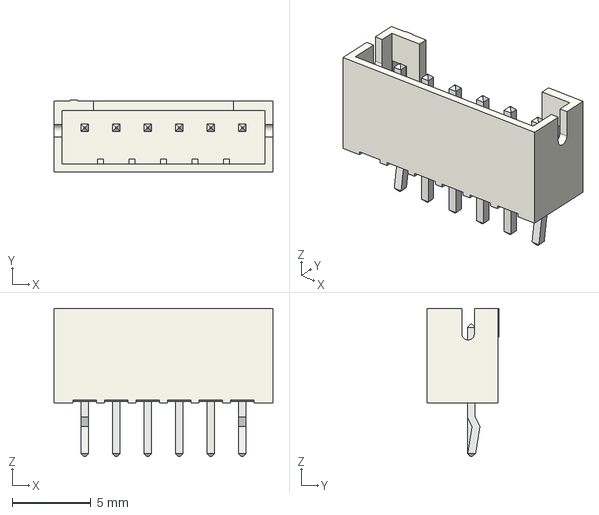
[picture p73: CAD file, 2026-07-23]
3dmodels/connectors/B6B-PH-K-S.step
13.9 x 4.55 x 9.40 mm
