blakhall/Kicad/3dmodels/connectors/B3B-PH-K-S.step

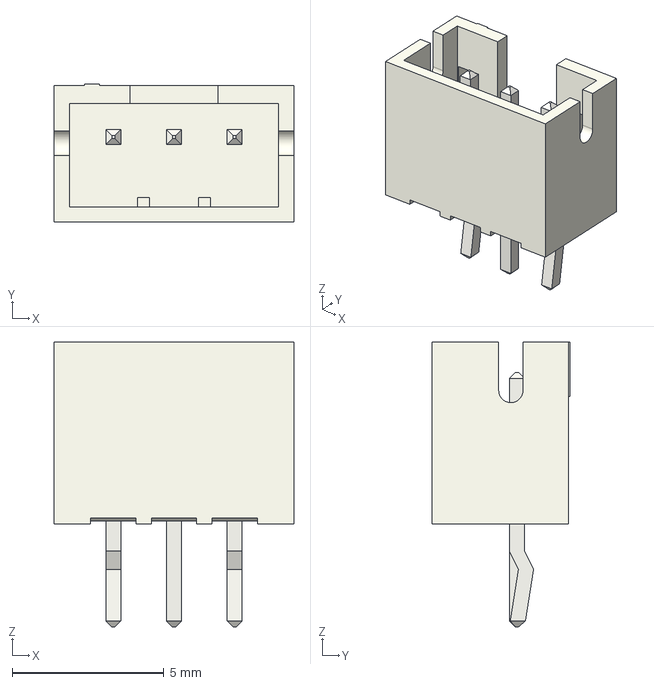
[picture p74: CAD file, 2026-07-23]
3dmodels/connectors/B3B-PH-K-S.step
7.90 x 4.55 x 9.40 mm
