blakhall/Kicad/3dmodels/power_gen/KMH_635x100-Body.step

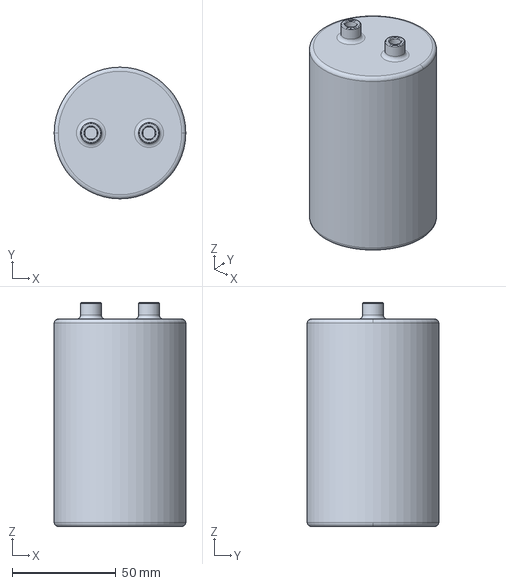
[picture p75: CAD file, 2025-08-17]
3dmodels/power_gen/KMH_635x100-Body.step
63.5 x 63.5 x 108.0 mm
