blakhall/Kicad/3dmodels/common/DE2E3SA222MA3BY02F.step

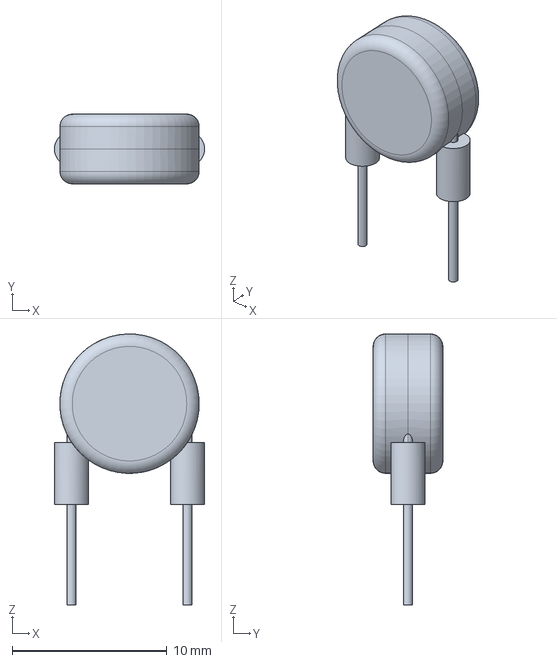
[picture p76: CAD file, 2026-09-08]
3dmodels/common/DE2E3SA222MA3BY02F.step
9.70 x 4.50 x 17.5 mm
