blakhall/Kicad/3dmodels/connectors/S4B-PH-K-S.step

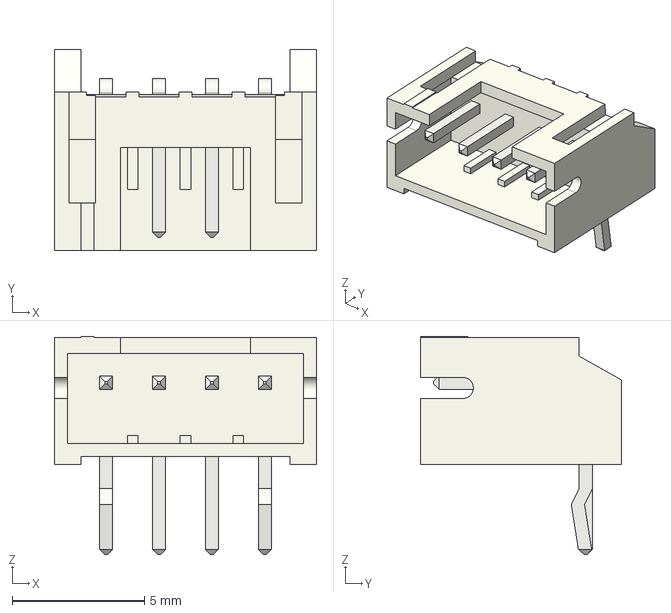
[picture p77: CAD file, 2026-07-09]
3dmodels/connectors/S4B-PH-K-S.step
9.90 x 7.60 x 8.25 mm
