blakhall/Kicad/3dmodels/power_gen/infineon-pg-hdsop-22-3-3d-01-stp-package-en.stp

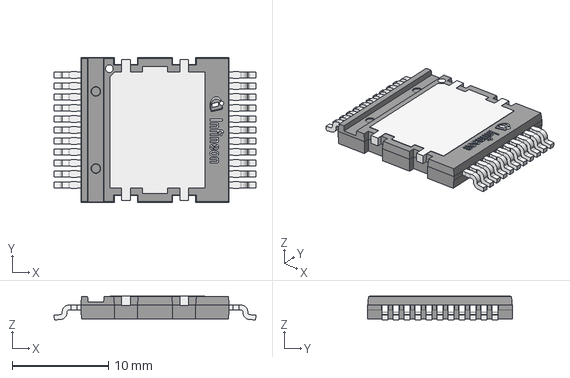
[picture p78: CAD file, 2025-08-12]
3dmodels/power_gen/infineon-pg-hdsop-22-3-3d-01-stp-package-en.stp
21.0 x 15.0 x 2.49 mm
