blakhall/Kicad/3dmodels/common/SC-07-10J.step

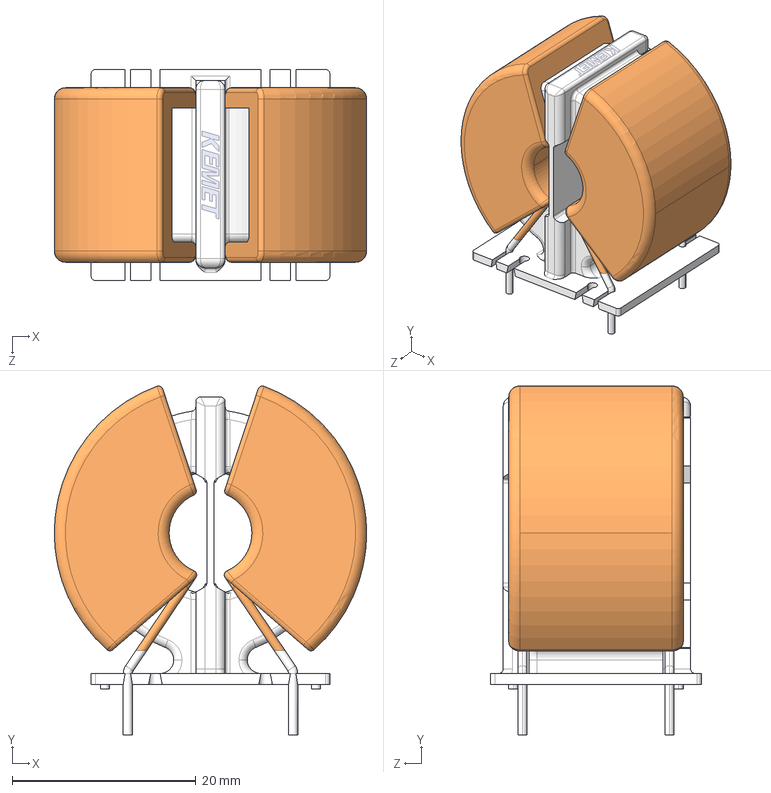
[picture p79: CAD file, 2026-09-08]
3dmodels/common/SC-07-10J.step
34.0 x 38.0 x 23.0 mm
