blakhall/Kicad/3dmodels/connectors/USB4125-GF-A_REVA2.step

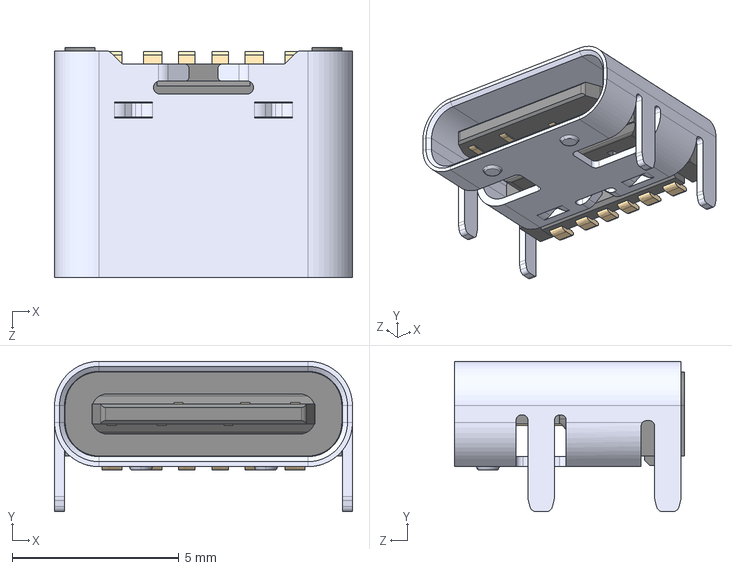
[picture p80: CAD file, 2025-09-30]
3dmodels/connectors/USB4125-GF-A_REVA2.step
8.94 x 4.51 x 6.90 mm
