blakhall/Kicad/3dmodels/power_gen/infineon-pg-lhdso-10-3-3d-01-stp-package-en.stp

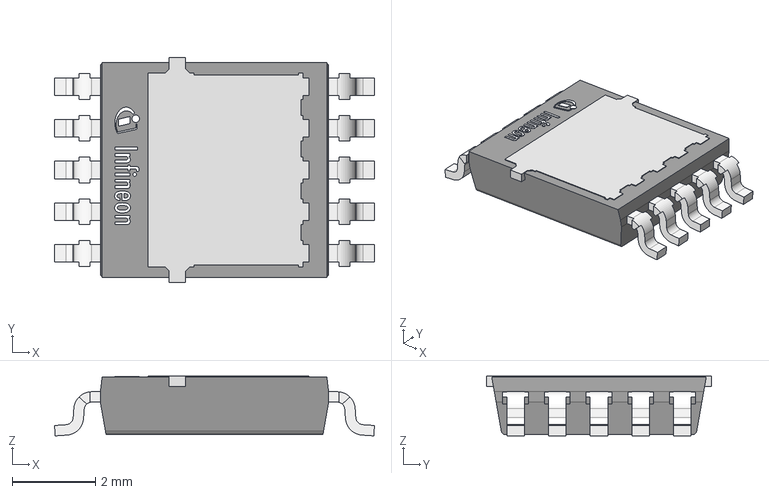
[picture p81: CAD file, 2025-07-16]
3dmodels/power_gen/infineon-pg-lhdso-10-3-3d-01-stp-package-en.stp
7.68 x 5.41 x 1.44 mm
