blakhall/Kicad/3dmodels/connectors/G-107-0513.step

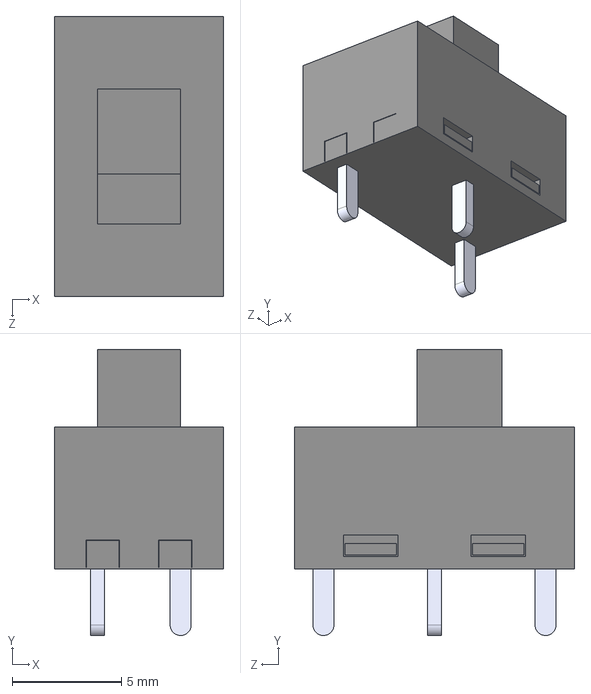
[picture p82: CAD file, 2025-09-30]
3dmodels/connectors/G-107-0513.step
7.75 x 13.1 x 12.8 mm
