blakhall/Kicad/3dmodels/power_gen/SOT-227.stp

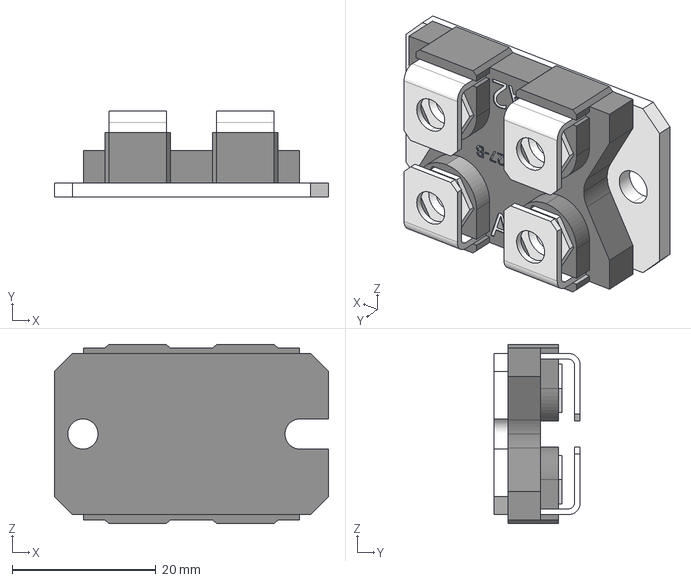
[picture p83: CAD file, 2025-07-03]
3dmodels/power_gen/SOT-227.stp
38.1 x 12.0 x 24.9 mm
