blakhall/Kicad/3dmodels/connectors/User Library-SMAW250-04G.step

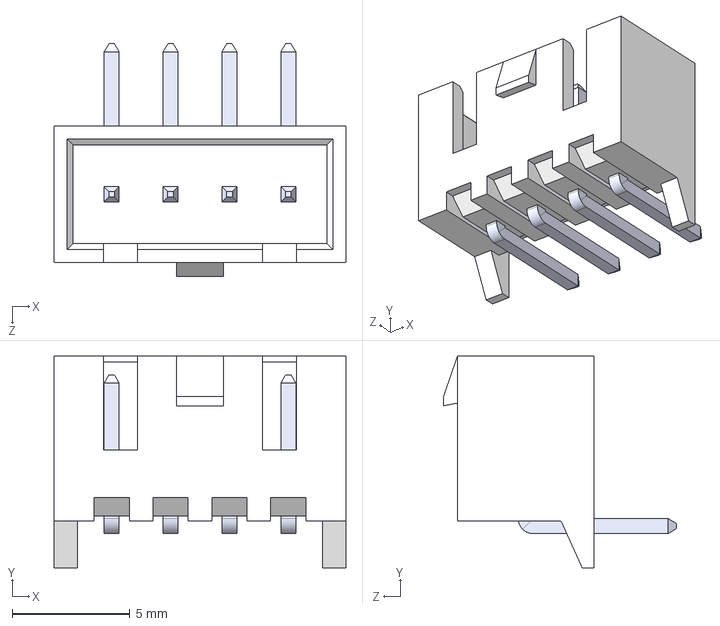
[picture p84: CAD file, 2025-09-19]
3dmodels/connectors/User Library-SMAW250-04G.step
12.4 x 9.00 x 9.89 mm
