blakhall/Kicad/3dmodels/power_gen/power_module_62mm.stp

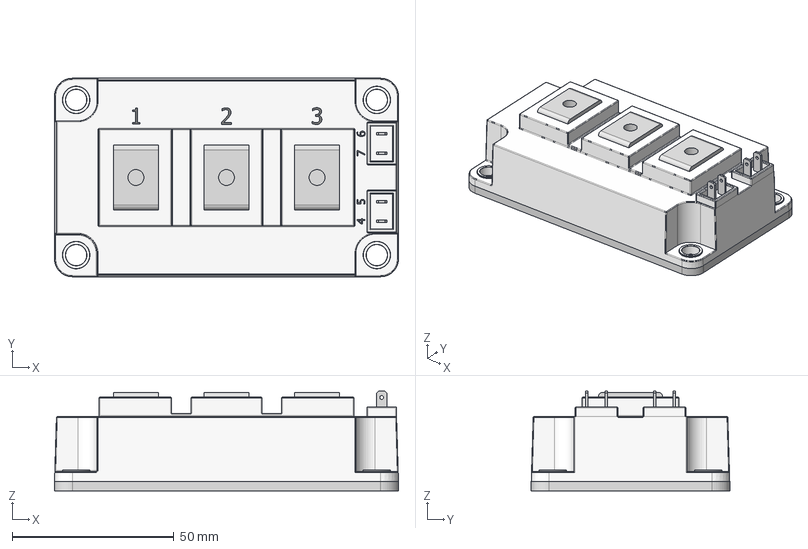
[picture p85: CAD file, 2025-07-03]
3dmodels/power_gen/power_module_62mm.stp
106.4 x 61.4 x 30.9 mm
62mm_Bodenplatte
62mm_Plastikgehäuse
62mm_Hauptkontakte x 3
62mm_Nebenkontakte x 4
