blakhall/Kicad/3dmodels/connectors/User Library-SMAW250-07G.step

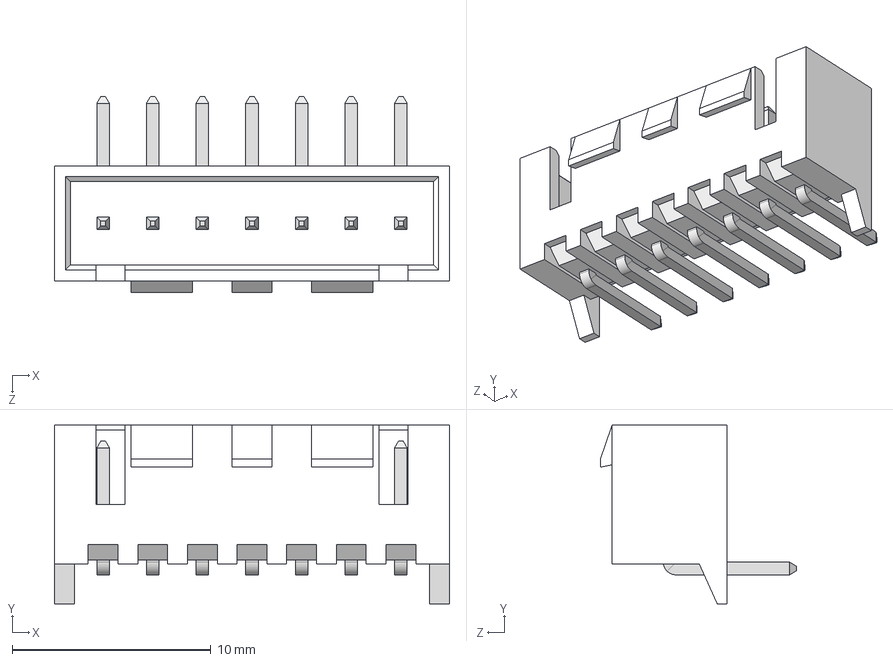
[picture p86: CAD file, 2025-09-19]
3dmodels/connectors/User Library-SMAW250-07G.step
19.9 x 9.00 x 9.89 mm
