blakhall/Kicad/3dmodels/common/DE2E3SA472MA3BY02F.step

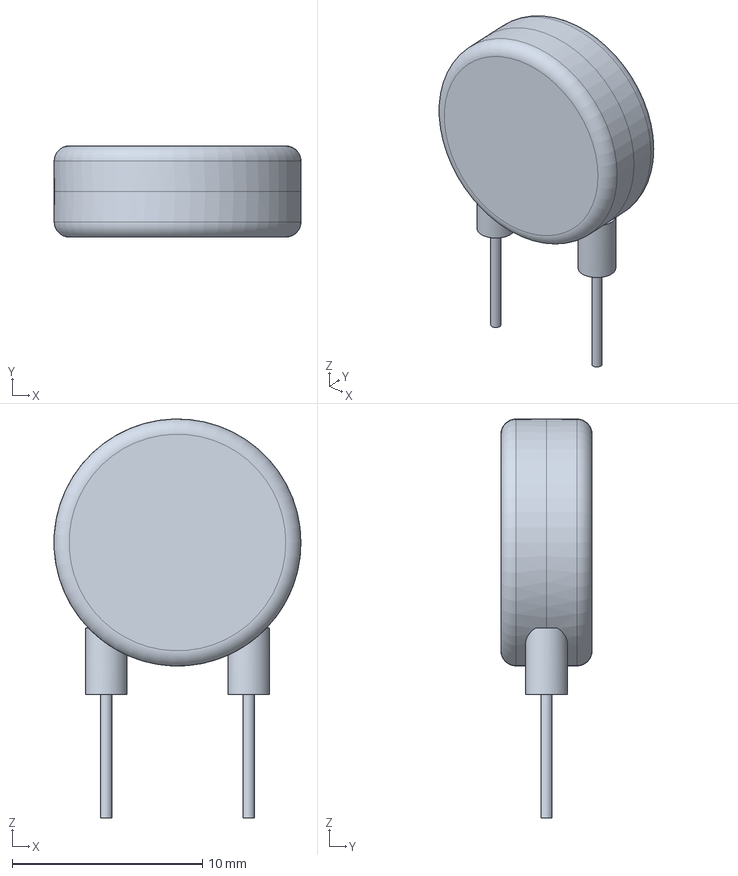
[picture p87: CAD file, 2026-09-08]
3dmodels/common/DE2E3SA472MA3BY02F.step
13.0 x 4.80 x 21.0 mm
