blakhall/Kicad/3dmodels/connectors/User Library-SMAW250-08G.step

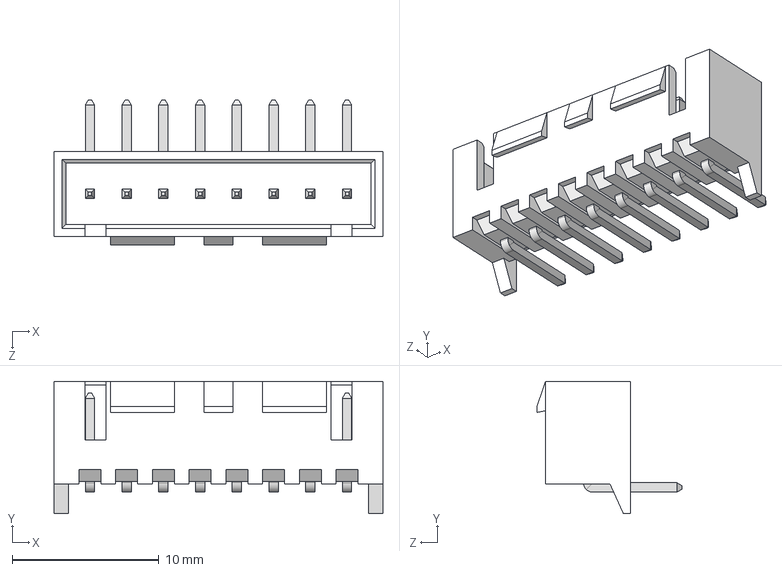
[picture p88: CAD file, 2025-09-19]
3dmodels/connectors/User Library-SMAW250-08G.step
22.4 x 9.00 x 9.89 mm
