blakhall/Kicad/3dmodels/connectors/User Library-SMAW250-10G.step

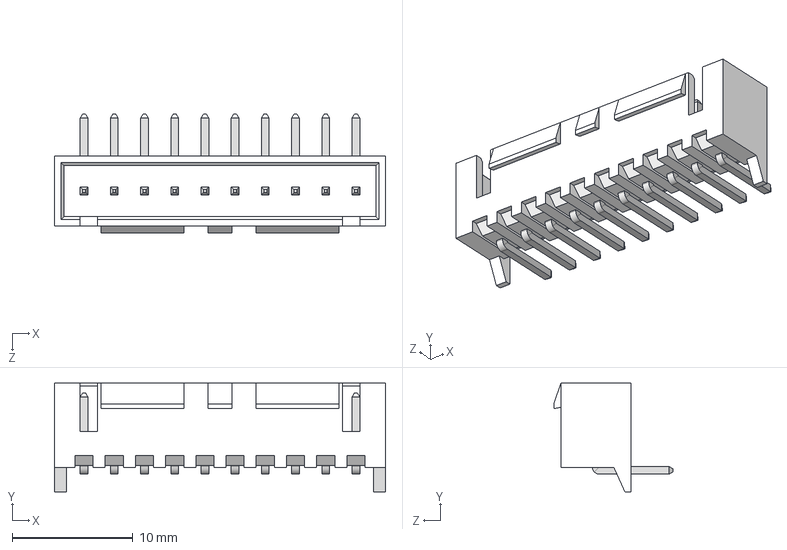
[picture p89: CAD file, 2025-09-19]
3dmodels/connectors/User Library-SMAW250-10G.step
27.4 x 9.00 x 9.89 mm
