blakhall/Kicad/3dmodels/connectors/User Library-SMAW250-02G.step

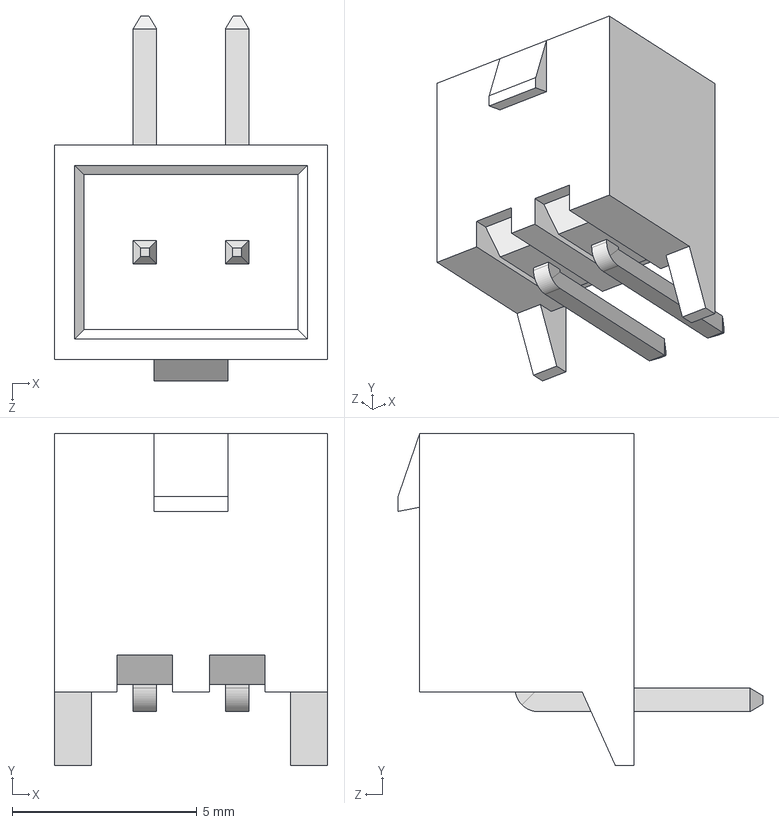
[picture p90: CAD file, 2025-09-19]
3dmodels/connectors/User Library-SMAW250-02G.step
7.40 x 9.00 x 9.89 mm
