blakhall/Kicad/3dmodels/connectors/User Library-SMAW250-03G.step

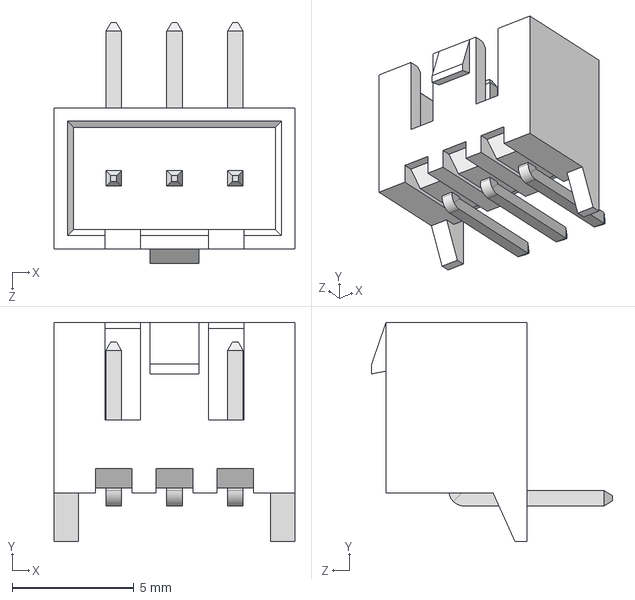
[picture p91: CAD file, 2025-09-19]
3dmodels/connectors/User Library-SMAW250-03G.step
9.90 x 9.00 x 9.89 mm
