blakhall/Kicad/3dmodels/connectors/User Library-SMAW250-12G.step

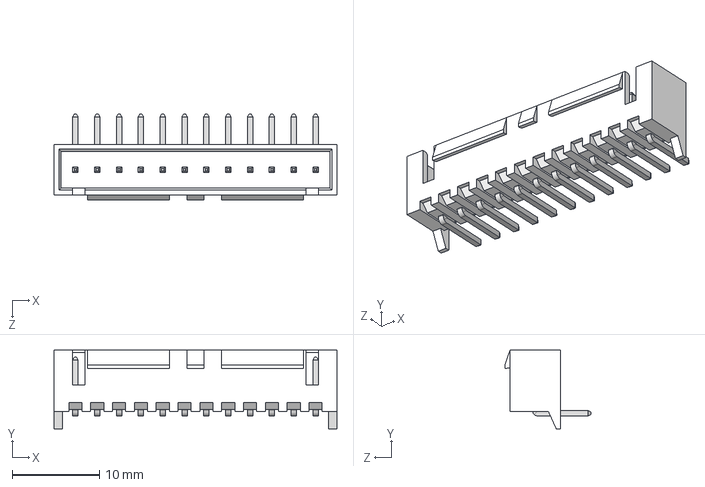
[picture p92: CAD file, 2025-09-19]
3dmodels/connectors/User Library-SMAW250-12G.step
32.4 x 9.00 x 9.89 mm
