blakhall/Kicad/3dmodels/connectors/User Library-SMAW250-05G.step

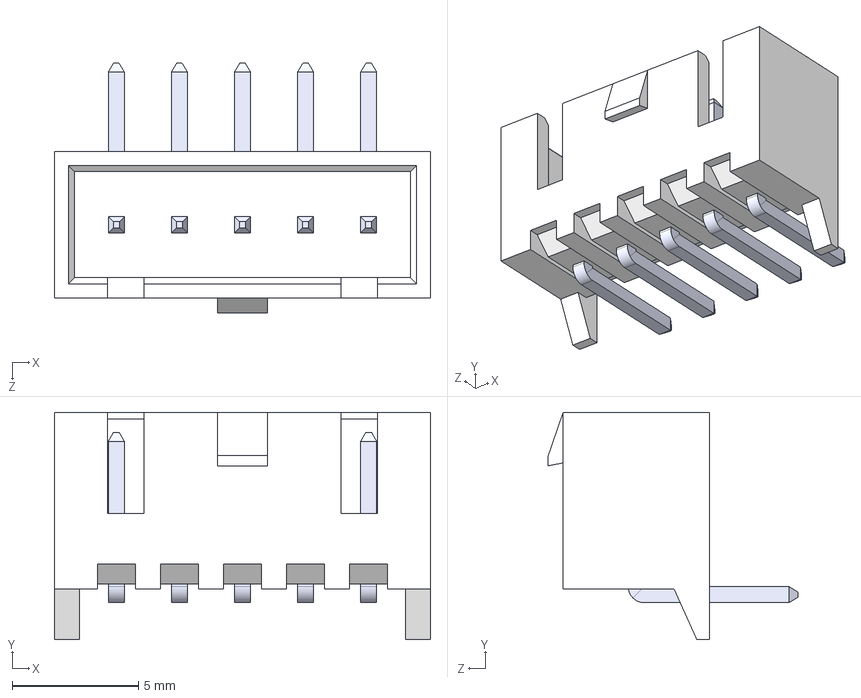
[picture p93: CAD file, 2025-09-19]
3dmodels/connectors/User Library-SMAW250-05G.step
14.9 x 9.00 x 9.89 mm
