blakhall/Kicad/3dmodels/connectors/User Library-SMAW250-09G.step

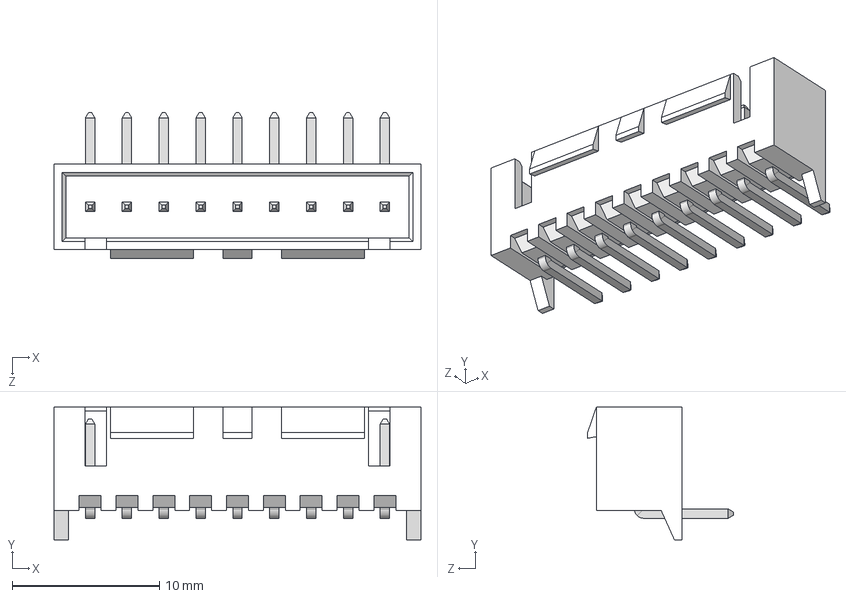
[picture p94: CAD file, 2025-09-19]
3dmodels/connectors/User Library-SMAW250-09G.step
24.9 x 9.00 x 9.89 mm
