blakhall/Kicad/3dmodels/connectors/User Library-SMAW250-06G.step

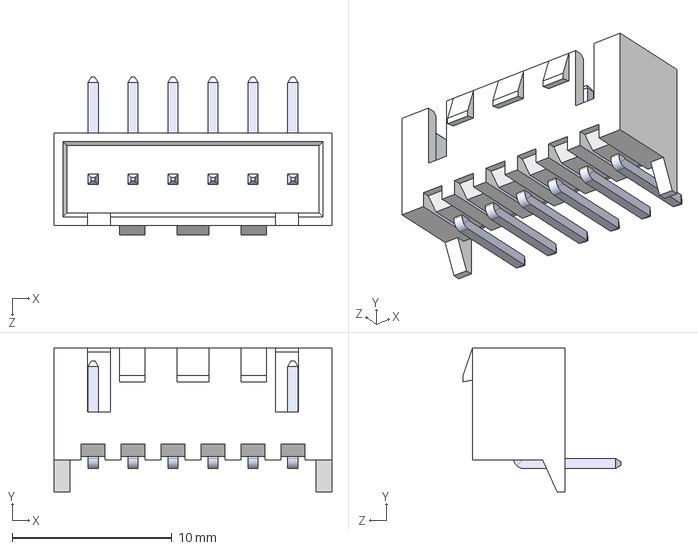
[picture p95: CAD file, 2025-09-19]
3dmodels/connectors/User Library-SMAW250-06G.step
17.4 x 9.00 x 9.89 mm
