blakhall/Kicad/3dmodels/connectors/YW396_07.step

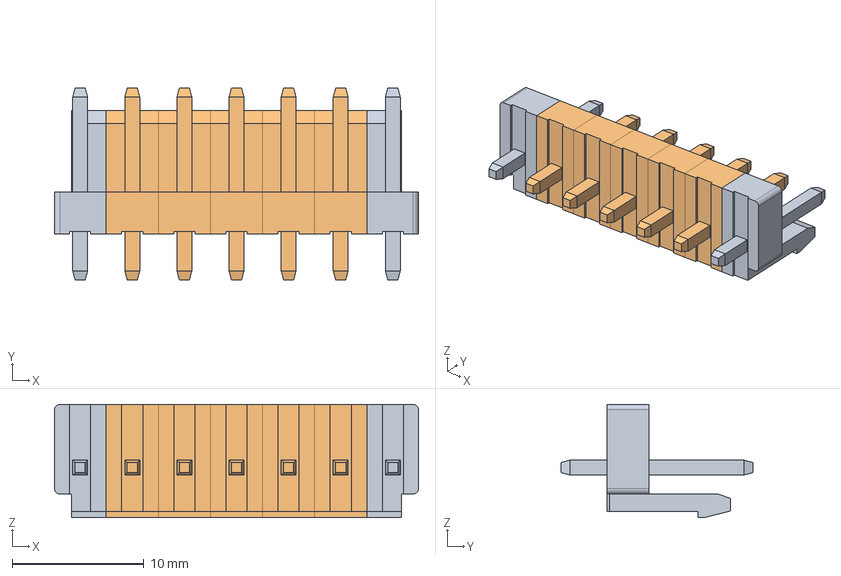
[picture p96: CAD file, 2025-08-22]
3dmodels/connectors/YW396_07.step
27.7 x 14.6 x 8.60 mm
