blakhall/Kicad/3dmodels/connectors/YW396_04.step

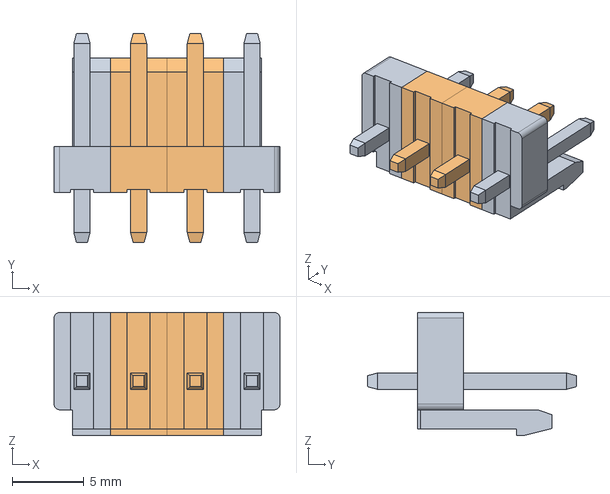
[picture p97: CAD file, 2025-08-22]
3dmodels/connectors/YW396_04.step
15.8 x 14.6 x 8.60 mm
