blakhall/Kicad/3dmodels/connectors/YW396_05.step

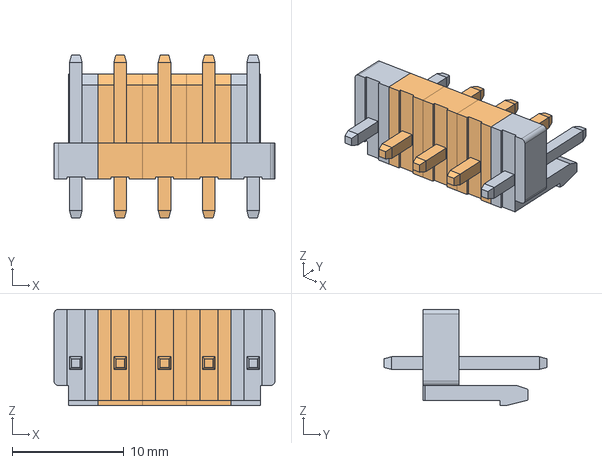
[picture p98: CAD file, 2025-08-22]
3dmodels/connectors/YW396_05.step
19.7 x 14.6 x 8.60 mm
