blakhall/Kicad/3dmodels/connectors/YW396_03.step

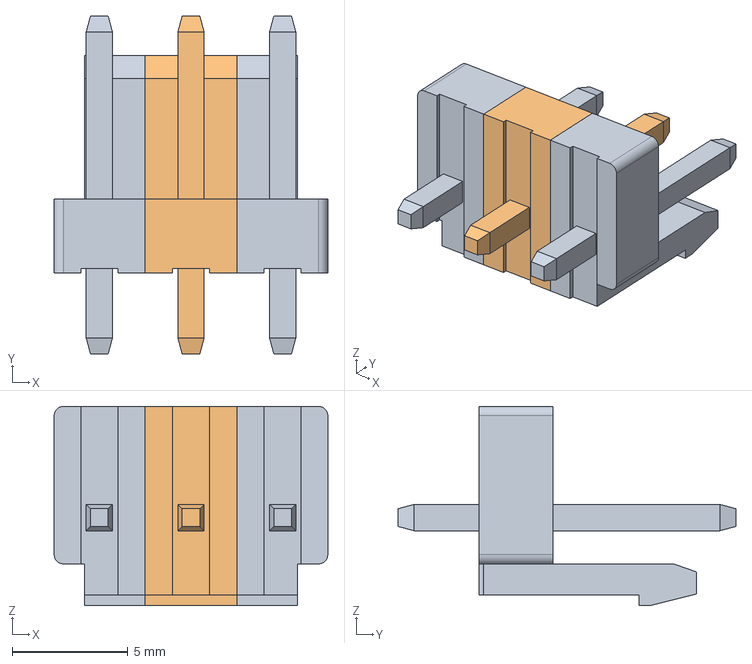
[picture p99: CAD file, 2025-08-22]
3dmodels/connectors/YW396_03.step
11.8 x 14.6 x 8.60 mm
