blakhall/Kicad/3dmodels/connectors/YW396_02.step

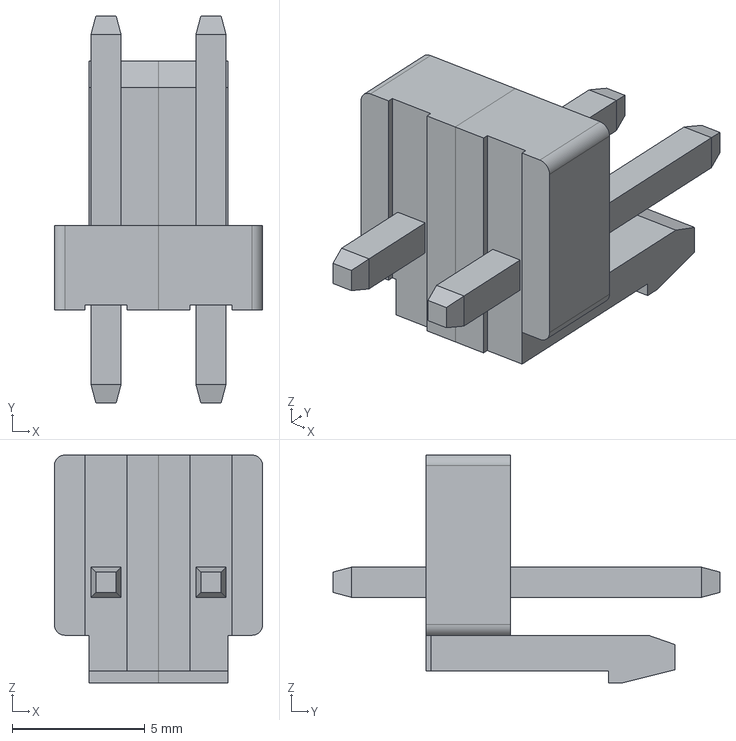
[picture p100: CAD file, 2025-08-22]
3dmodels/connectors/YW396_02.step
7.86 x 14.6 x 8.60 mm
