blakhall/Kicad/3dmodels/connectors/YW396_08.step

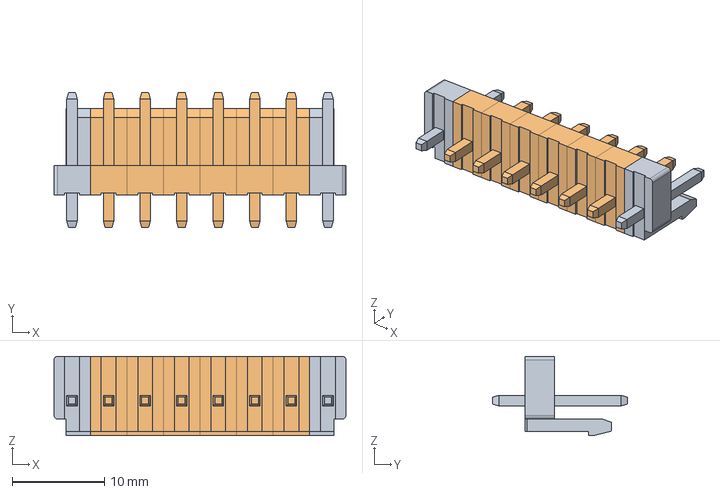
[picture p101: CAD file, 2025-08-22]
3dmodels/connectors/YW396_08.step
31.6 x 14.6 x 8.60 mm
