blakhall/Kicad/3dmodels/connectors/YW396_10.step

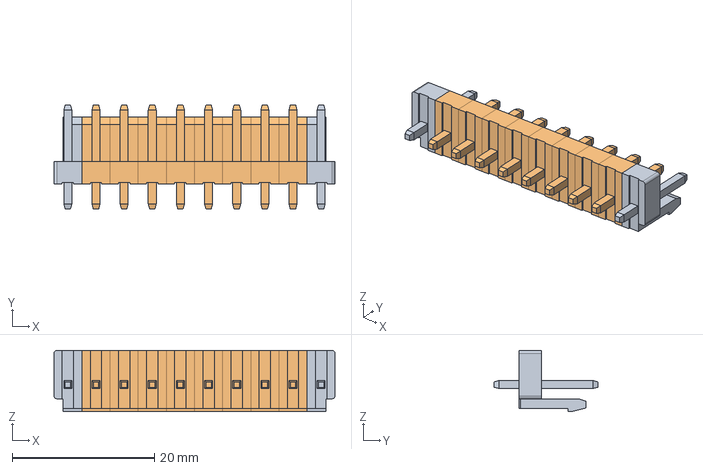
[picture p102: CAD file, 2025-08-22]
3dmodels/connectors/YW396_10.step
39.5 x 14.6 x 8.60 mm
