blakhall/Kicad/3dmodels/connectors/YW396_09.step

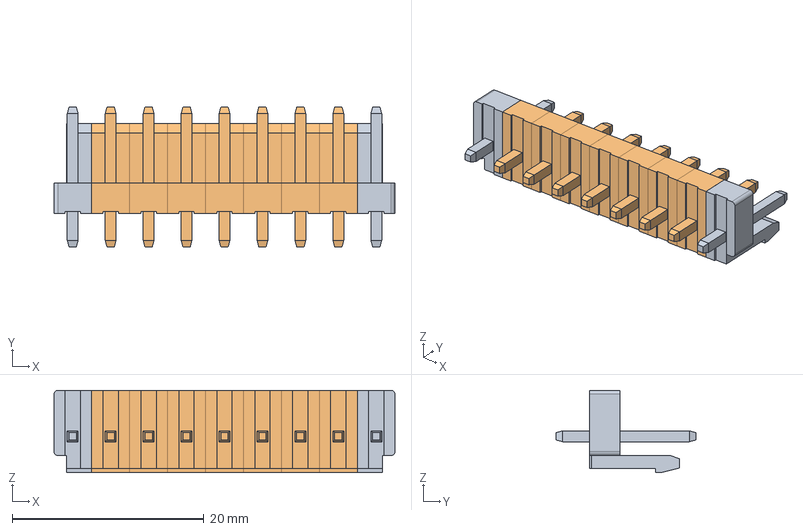
[picture p103: CAD file, 2025-08-22]
3dmodels/connectors/YW396_09.step
35.6 x 14.6 x 8.60 mm
