blakhall/Kicad/3dmodels/connectors/YW396_06.step

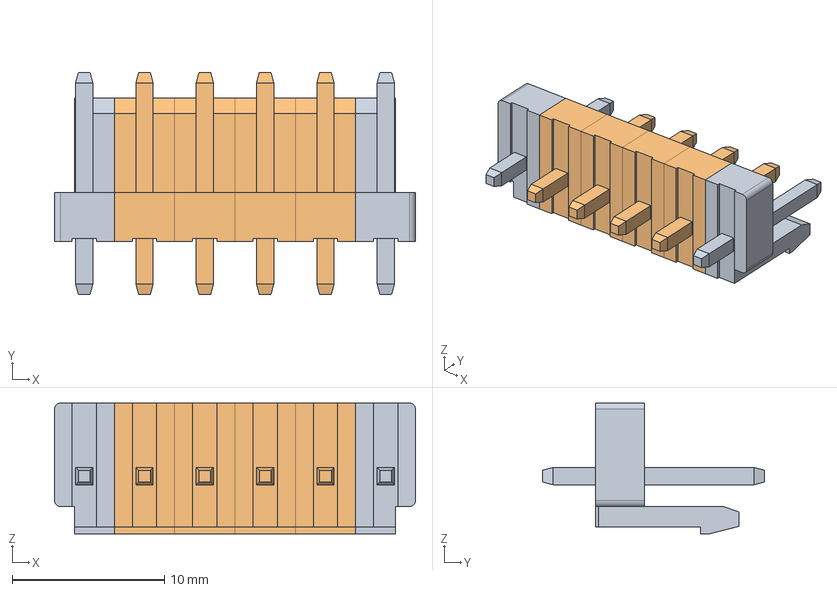
[picture p104: CAD file, 2025-08-22]
3dmodels/connectors/YW396_06.step
23.7 x 14.6 x 8.60 mm
