blakhall/Kicad/3dmodels/connectors/smw250-12_p2-5_l32-4_w5-8_h7.stp

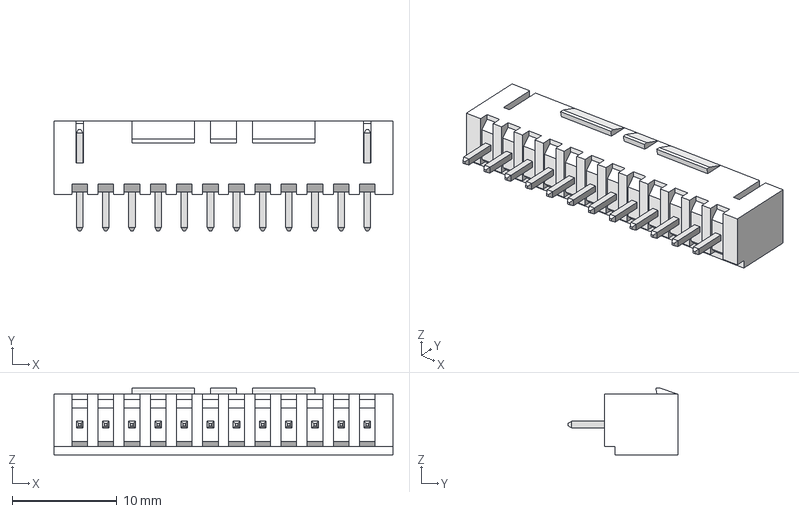
[picture p106: CAD file, 2025-08-12]
3dmodels/connectors/smw250-12_p2-5_l32-4_w5-8_h7.stp
32.4 x 10.5 x 6.39 mm
