blakhall/Kicad/3dmodels/connectors/smw250-10_p2-5_l27-4_w5-8_h7.stp

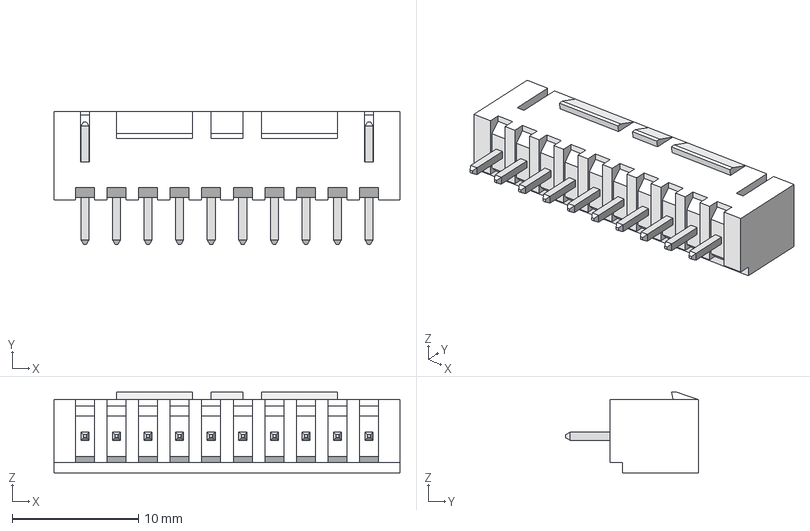
[picture p107: CAD file, 2025-08-12]
3dmodels/connectors/smw250-10_p2-5_l27-4_w5-8_h7.stp
27.4 x 10.5 x 6.39 mm
