blakhall/Kicad/3dmodels/connectors/smw250-11_p2-5_l29-9_w5-8_h7.stp

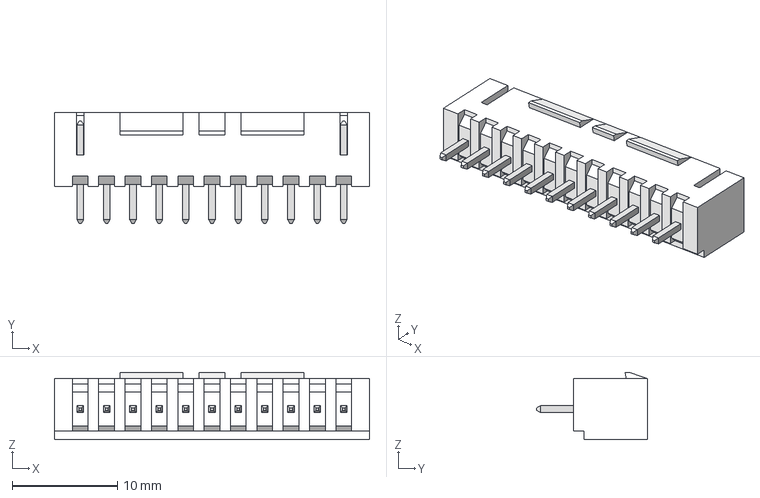
[picture p109: CAD file, 2025-08-12]
3dmodels/connectors/smw250-11_p2-5_l29-9_w5-8_h7.stp
29.9 x 10.5 x 6.39 mm
