blakhall/Kicad/3dmodels/connectors/smw250-13_p2-5_l34-9_w5-8_h7.stp

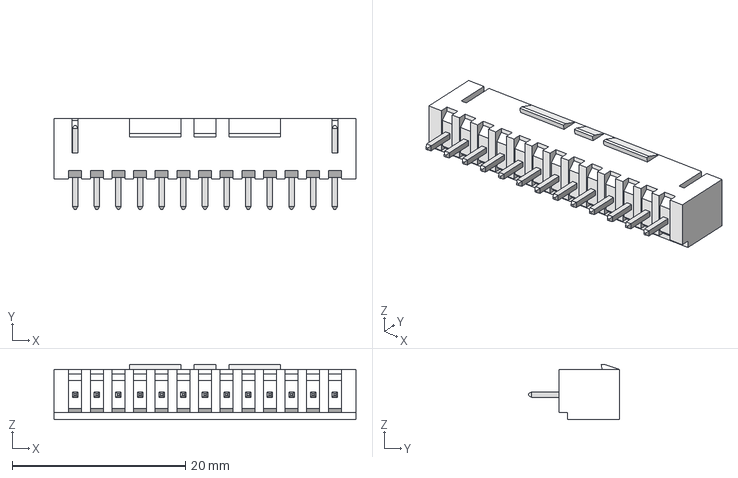
[picture p111: CAD file, 2025-08-12]
3dmodels/connectors/smw250-13_p2-5_l34-9_w5-8_h7.stp
34.9 x 10.5 x 6.39 mm
