blakhall/Kicad/3dmodels/connectors/smw250-02_p2-5_l7-4_w5-8_h7.stp

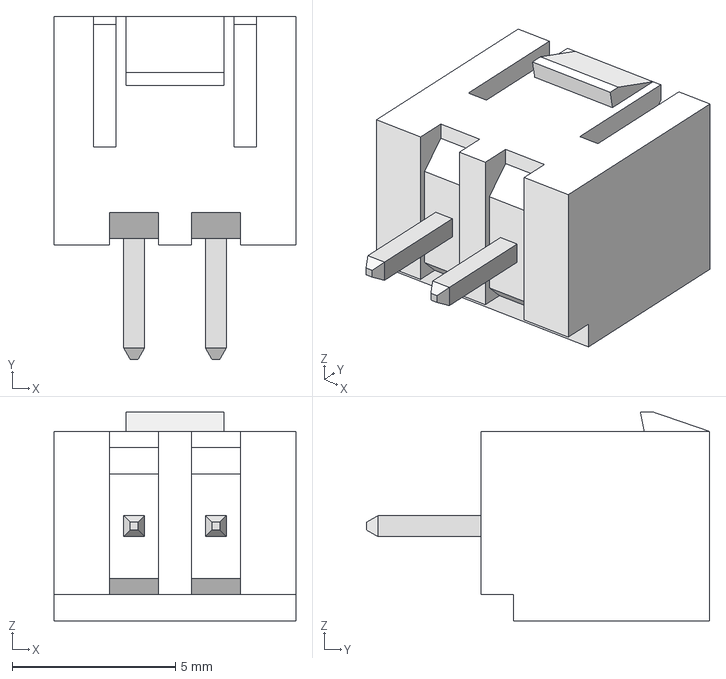
[picture p114: CAD file, 2025-08-12]
3dmodels/connectors/smw250-02_p2-5_l7-4_w5-8_h7.stp
7.40 x 10.5 x 6.39 mm
