blakhall/Kicad/3dmodels/connectors/smw250-03_p2-5_l9-9_w5-8_h7.stp

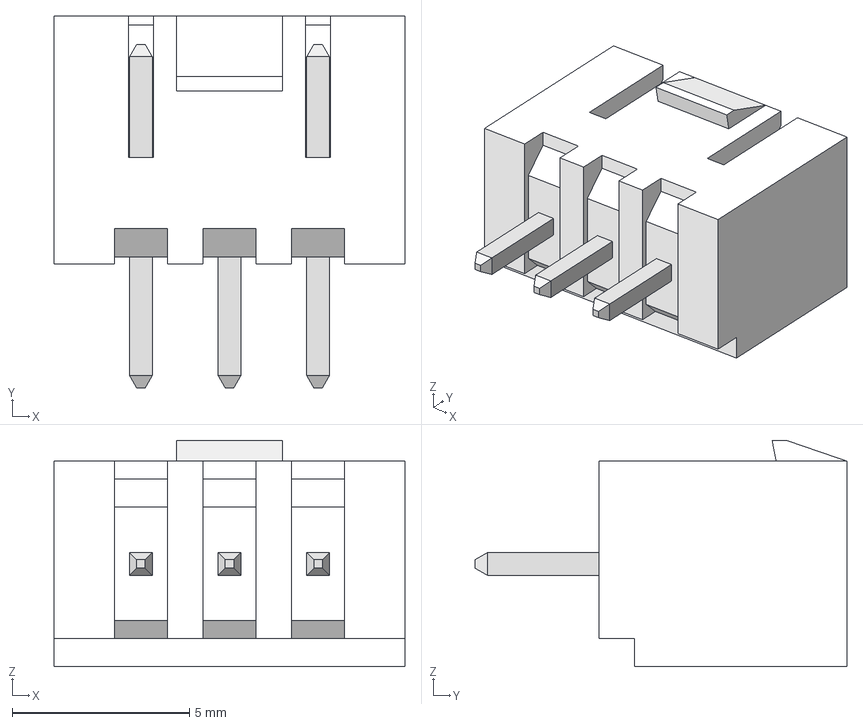
[picture p116: CAD file, 2025-08-12]
3dmodels/connectors/smw250-03_p2-5_l9-9_w5-8_h7.stp
9.90 x 10.5 x 6.39 mm
