blakhall/Kicad/3dmodels/connectors/smw250-09_p2-5_l24-9_w5-8_h7.stp

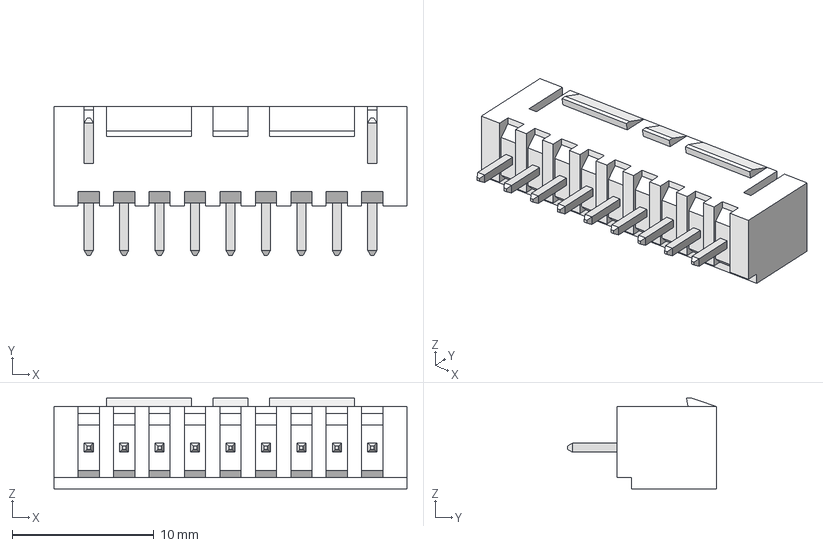
[picture p117: CAD file, 2025-08-12]
3dmodels/connectors/smw250-09_p2-5_l24-9_w5-8_h7.stp
24.9 x 10.5 x 6.39 mm
