blakhall/Kicad/3dmodels/connectors/smw250-07_p2-5_l19-9_w5-8_h7.stp

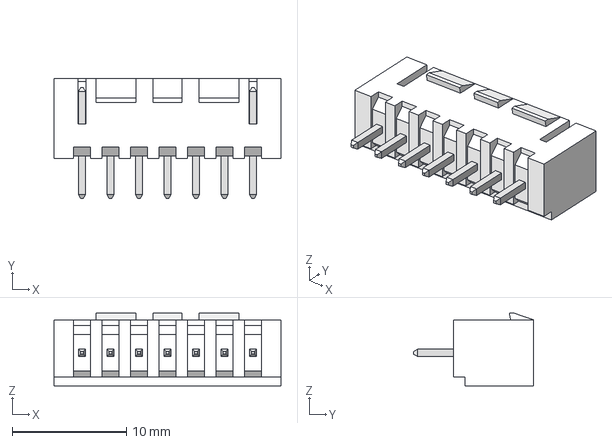
[picture p118: CAD file, 2025-08-12]
3dmodels/connectors/smw250-07_p2-5_l19-9_w5-8_h7.stp
19.9 x 10.5 x 6.39 mm
