blakhall/Kicad/schematic/main/MAX20801.kicad_sch

## KiCad design schematic/main/MAX20801.kicad_sch (2026-04-12, an earlier design)

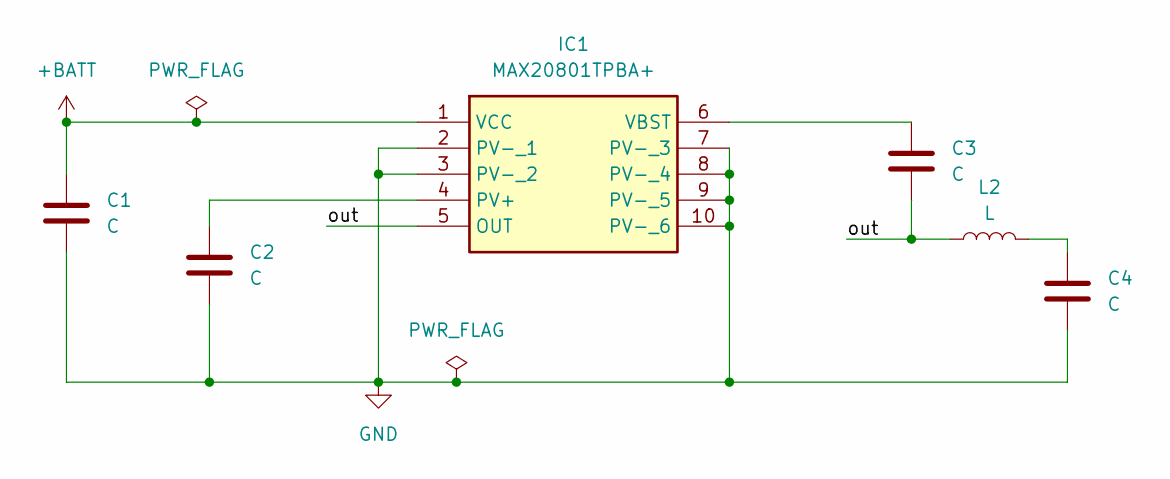
[picture p119: schematic MAX20801.kicad_sch]

Parts:
C1, C2, C3, C4: C; Part Number any
IC1: MAX20801TPBA+; MAX20801TPBA; Mouser Part Number 700-MAX20801TPBA+
L2: L

Connections:
+BATT: C1.1, IC1.1 (VCC)
GND: C1.2, C2.2, C4.2, IC1.2 (PV-_1), IC1.3 (PV-_2), IC1.7 (PV-_3), IC1.8 (PV-_4), IC1.9 (PV-_5), IC1.10 (PV-_6)
unnamed: C2.1, IC1.4 (PV+)
unnamed: C3.1, IC1.6 (VBST)
unnamed: C4.1, L2.2
out: C3.2, IC1.5 (OUT), L2.1
