blakhall/Kicad/schematic/main/analog_buffer.kicad_sch

## KiCad design schematic/main/analog_buffer.kicad_sch (2026-04-12, an earlier design)

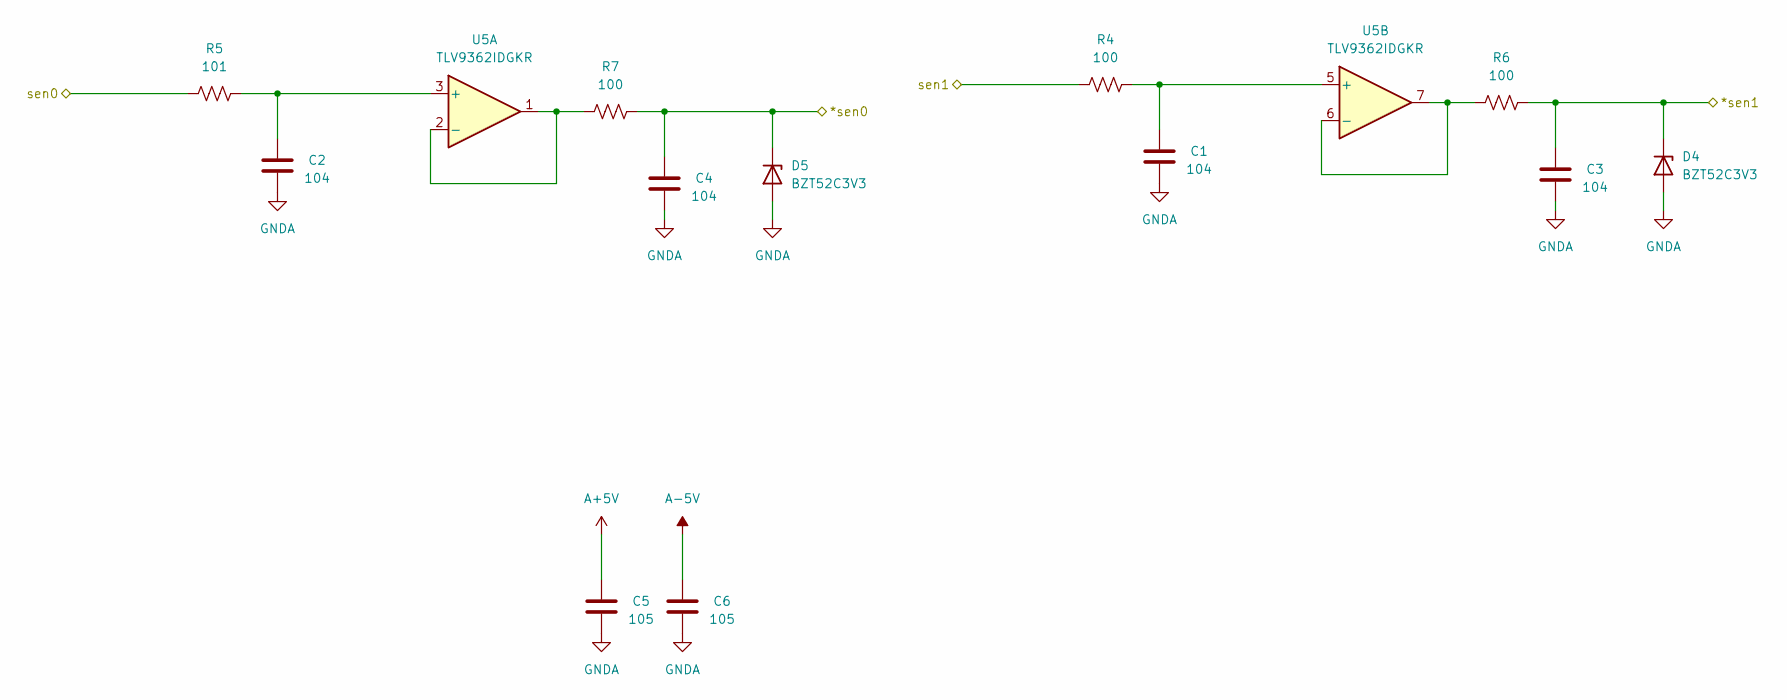
[picture p120: schematic analog_buffer.kicad_sch]

Parts:
C1, C2, C3, C4: 104; C_0603_1608Metric; Part Number any
C5, C6: 105; C_0603_1608Metric; Part Number any
D4, D5: BZT52C3V3; D_SOD-123
R4, R6, R7: 100; R_0603_1608Metric
R5: 101; R_0603_1608Metric
U5: TLV9362IDGKR; VSSOP-8_3x3mm_P0.65mm

Connections:
A+5V: C5.2
A-5V: C6.2
GNDA: C1.1, C2.1, C3.1, C4.1, C5.1, C6.1, D4.2 (A), D5.2 (A)
unnamed: C1.2, R4.2, U5.5 (+)
unnamed: C2.2, R5.2, U5.3 (+)
unnamed: R6.1, U5.6 (-), U5.7
unnamed: R7.1, U5.1, U5.2 (-)
sen0: C4.2, D5.1 (K), R5.1, R7.2
sen1: C3.2, D4.1 (K), R4.1, R6.2
