blakhall/Kicad/schematic/main/high_voltage.kicad_sch

## KiCad design schematic/main/high_voltage.kicad_sch (2026-04-12, an earlier design)

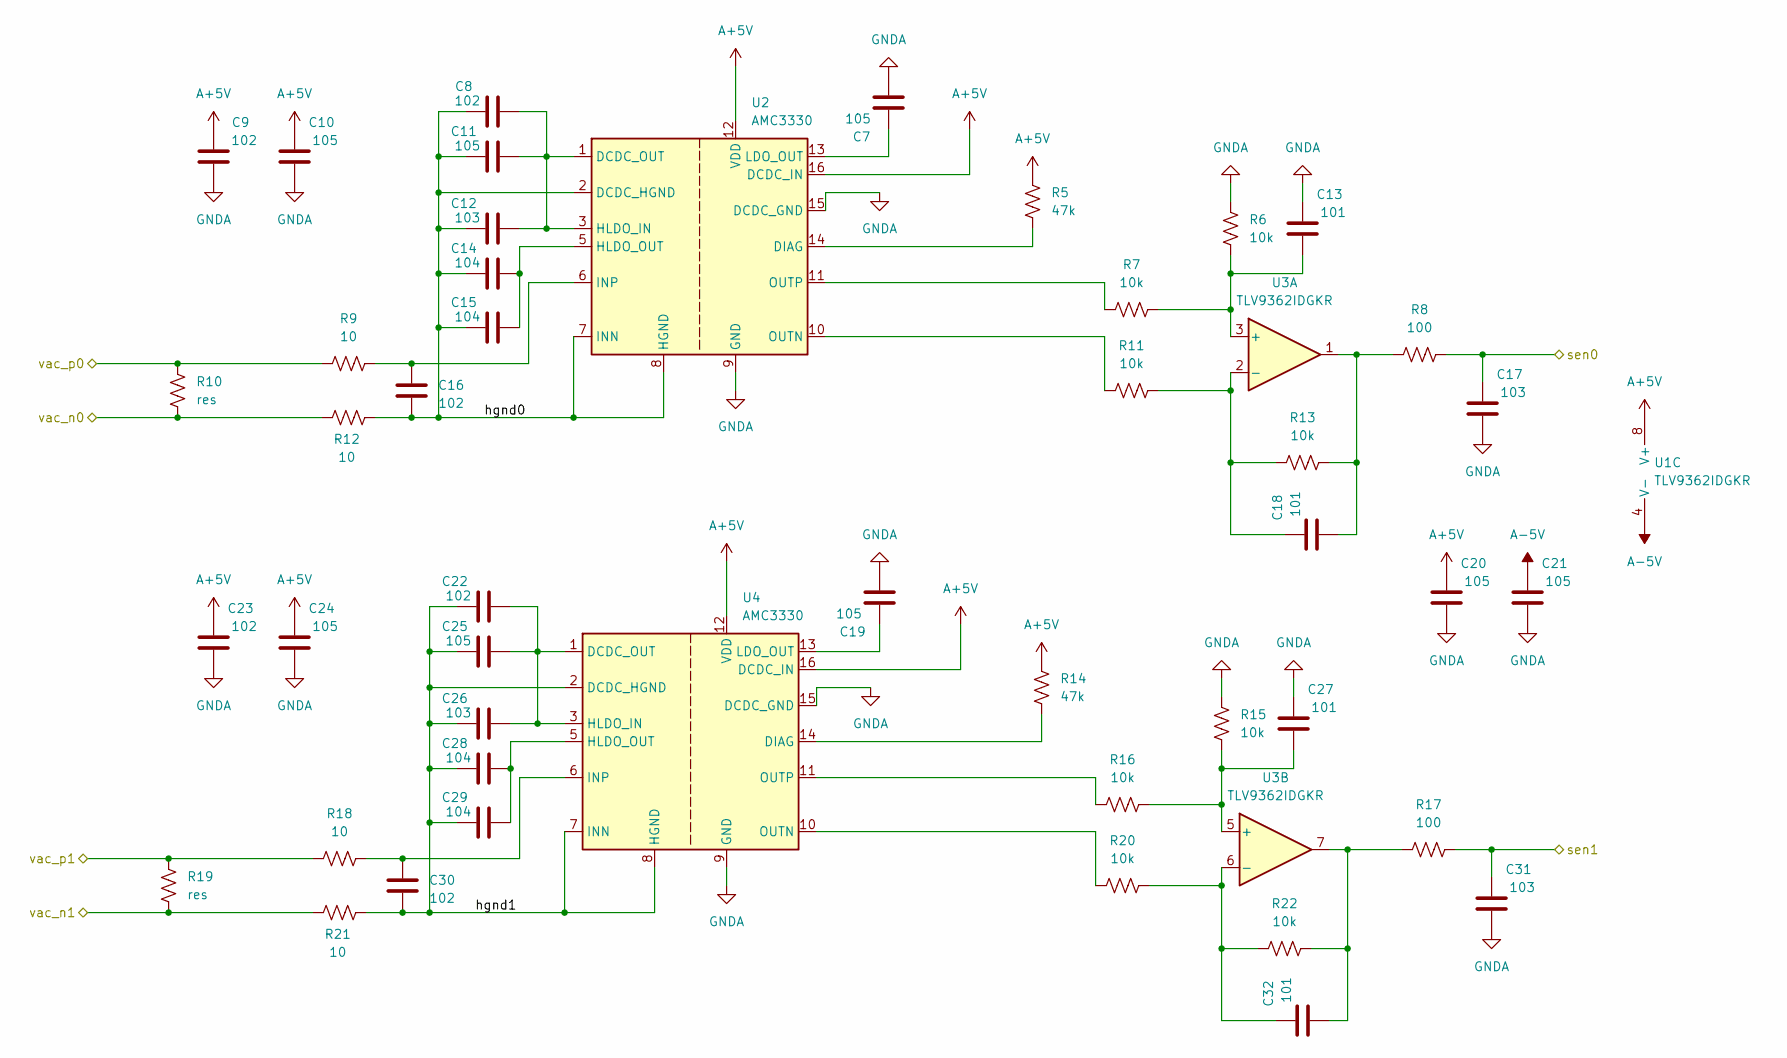
[picture p121: schematic high_voltage.kicad_sch]

Parts:
C7, C10, C11, C19, C20, C21, C24, C25: 105; C_0603_1608Metric; Part Number any
C8, C9, C16, C22, C23, C30: 102; C_0603_1608Metric; Part Number any
C12, C17, C26, C31: 103; C_0603_1608Metric; Part Number any
C13, C18, C27, C32: 101; C_0603_1608Metric; Part Number any
C14, C15, C28, C29: 104; C_0603_1608Metric; Part Number any
R5, R14: 47k; R_0603_1608Metric
R6, R7, R11, R13, R15, R16, R20, R22: 10k; R_0603_1608Metric
R8, R17: 100; R_0603_1608Metric
R9, R12, R18, R21: 10; R_0603_1608Metric
R10, R19: res; R_0603_1608Metric
U1, U3: TLV9362IDGKR; VSSOP-8_3x3mm_P0.65mm
U2, U4: AMC3330; SOIC-16W_7.5x10.3mm_P1.27mm

Connections:
A+5V: C9.1, C10.1, C20.1, C23.1, C24.1, R5.1, R14.1, U1.8 (V+), U2.12 (VDD), U2.16 (DCDC_IN), U4.12 (VDD), U4.16 (DCDC_IN)
A-5V: C21.1, U1.4 (V-)
GNDA: C7.2, C9.2, C10.2, C13.1, C17.2, C19.2, C20.2, C21.2, C23.2, C24.2, C27.1, C31.2, R6.2, R15.2, U2.9 (GND), U2.15 (DCDC_GND), U4.9 (GND), U4.15 (DCDC_GND)
unnamed: C7.1, U2.13 (LDO_OUT)
unnamed: C8.2, C11.2, C12.2, U2.1 (DCDC_OUT), U2.3 (HLDO_IN)
unnamed: C13.2, R6.1, R7.2, U3.3 (+)
unnamed: C14.2, C15.2, U2.5 (HLDO_OUT)
unnamed: C16.2, R9.2, U2.6 (INP)
unnamed: C18.1, R11.2, R13.1, U3.2 (-)
unnamed: C18.2, R8.1, R13.2, U3.1
unnamed: C19.1, U4.13 (LDO_OUT)
unnamed: C22.2, C25.2, C26.2, U4.1 (DCDC_OUT), U4.3 (HLDO_IN)
unnamed: C27.2, R15.1, R16.2, U3.5 (+)
unnamed: C28.2, C29.2, U4.5 (HLDO_OUT)
unnamed: C30.2, R18.2, U4.6 (INP)
unnamed: C32.1, R20.2, R22.1, U3.6 (-)
unnamed: C32.2, R17.1, R22.2, U3.7
unnamed: R5.2, U2.14 (DIAG)
unnamed: R7.1, U2.11 (OUTP)
unnamed: R11.1, U2.10 (OUTN)
unnamed: R14.2, U4.14 (DIAG)
unnamed: R16.1, U4.11 (OUTP)
unnamed: R20.1, U4.10 (OUTN)
hgnd0: C8.1, C11.1, C12.1, C14.1, C15.1, C16.1, R12.2, U2.2 (DCDC_HGND), U2.7 (INN), U2.8 (HGND)
hgnd1: C22.1, C25.1, C26.1, C28.1, C29.1, C30.1, R21.2, U4.2 (DCDC_HGND), U4.7 (INN), U4.8 (HGND)
sen0: C17.1, R8.2
sen1: C31.1, R17.2
vac_n0: R10.1, R12.1
vac_n1: R19.1, R21.1
vac_p0: R9.1, R10.2
vac_p1: R18.1, R19.2
