blakhall/Kicad/schematic/main/high_voltage_acpl.kicad_sch

## KiCad design schematic/main/high_voltage_acpl.kicad_sch (2026-04-12, an earlier design)

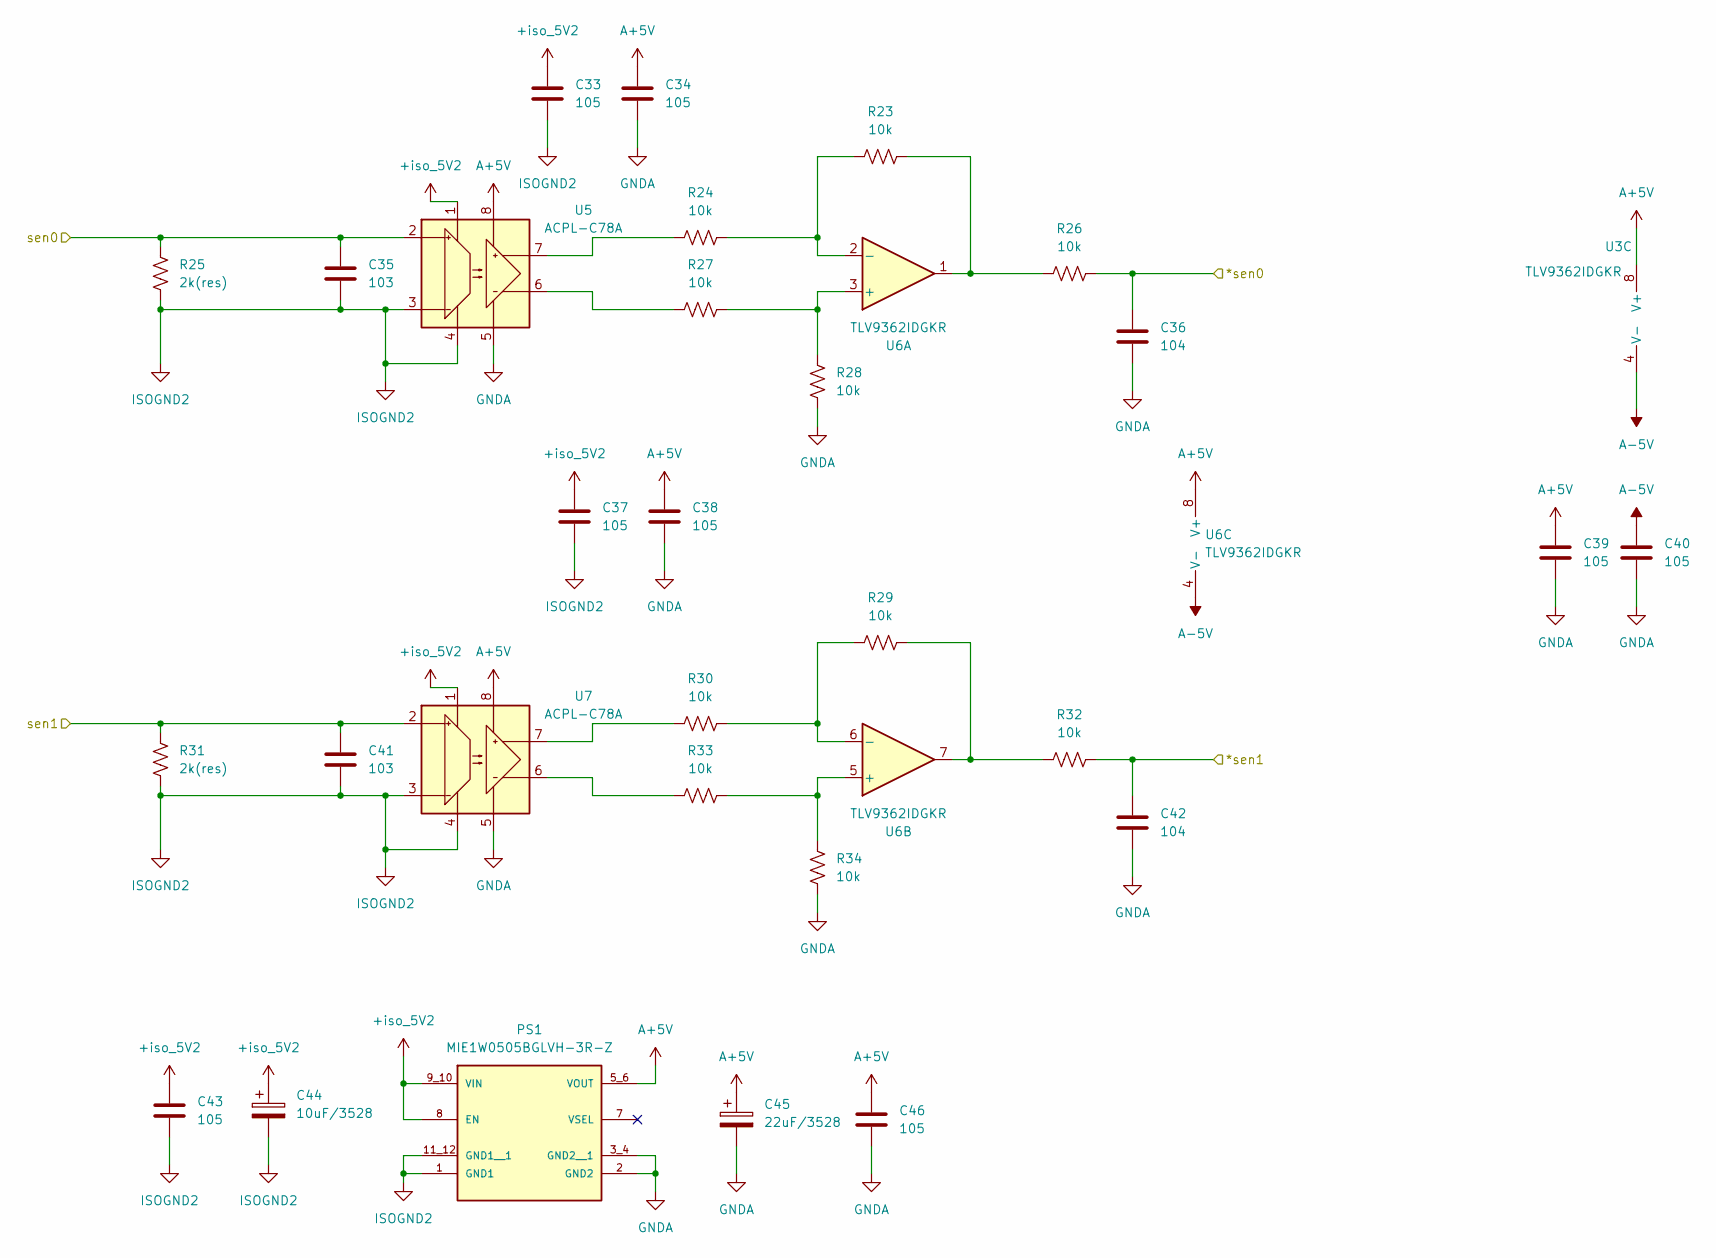
[picture p122: schematic high_voltage_acpl.kicad_sch]

Parts:
C33, C34, C37, C38, C39, C40, C43, C46: 105; C_0603_1608Metric; Part Number any
C35, C41: 103; C_0603_1608Metric; Part Number any
C36, C42: 104; C_0603_1608Metric; Part Number any
C44: 10uF/3528; CP_EIA-3528-12_Kemet-T
C45: 22uF/3528; CP_EIA-3528-12_Kemet-T
PS1: MIE1W0505BGLVH-3R-Z; CONV_MIE1W0505BGLVH-3R-Z; PARTREV 0.8
R23, R24, R26, R27, R28, R29, R30, R32, R33, R34: 10k; R_0603_1608Metric
R25, R31: 2k(res); R_0603_1608Metric
U3, U6: TLV9362IDGKR; VSSOP-8_3x3mm_P0.65mm
U5, U7: ACPL-C78A; SSO-8_6.8x5.9mm_P1.27mm_Clearance8mm

Connections:
+iso_5V2: C33.1, C37.1, C43.1, C44.1, PS1.8 (EN), PS1.9_10 (VIN), U5.1 (VDD1), U7.1 (VDD1)
A+5V: C34.1, C38.1, C39.1, C45.1, C46.1, PS1.5_6 (VOUT), U3.8 (V+), U5.8 (VDD2), U6.8 (V+), U7.8 (VDD2)
A-5V: C40.1, U3.4 (V-), U6.4 (V-)
GNDA: C34.2, C36.2, C38.2, C39.2, C40.2, C42.2, C45.2, C46.2, PS1.2 (GND2), PS1.3_4 (GND2__1), R28.1, R34.1, U5.5 (GND2), U7.5 (GND2)
ISOGND2: C33.2, C35.2, C37.2, C41.2, C43.2, C44.2, PS1.1 (GND1), PS1.11_12 (GND1__1), R25.2, R31.2, U5.3 (IN-), U5.4 (GND1), U7.3 (IN-), U7.4 (GND1)
unnamed: R23.1, R24.2, U6.2 (-)
unnamed: R23.2, R26.1, U6.1
unnamed: R24.1, U5.7 (OUT+)
unnamed: R27.1, U5.6 (OUT-)
unnamed: R27.2, R28.2, U6.3 (+)
unnamed: R29.1, R30.2, U6.6 (-)
unnamed: R29.2, R32.1, U6.7
unnamed: R30.1, U7.7 (OUT+)
unnamed: R33.1, U7.6 (OUT-)
unnamed: R33.2, R34.2, U6.5 (+)
sen0: C35.1, C36.1, R25.1, R26.2, U5.2 (IN+)
sen1: C41.1, C42.1, R31.1, R32.2, U7.2 (IN+)
