blakhall/Kicad/schematic/main/main.kicad_sch

## KiCad design schematic/main/main.kicad_sch (2026-04-12, an earlier design)

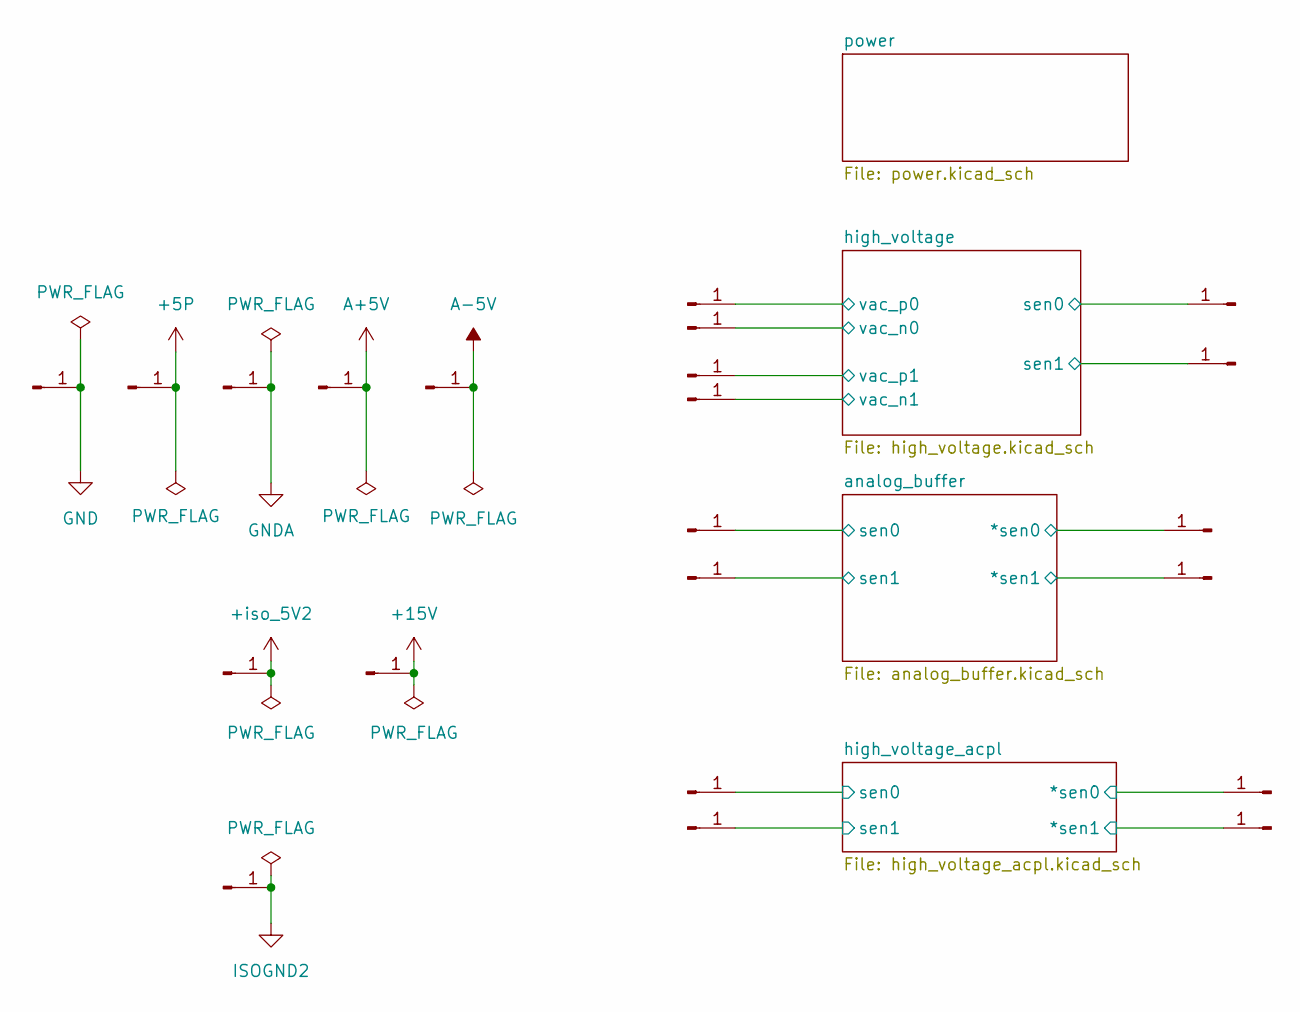
[picture p123: schematic main.kicad_sch]

Parts:
J1, J2, J3, J4, J5, J6, J7, J8, J9, J10, J11, J12, J13, J14, J15, J16, J17, J18, J19, J20, J21, J22: Conn_01x01_Pin

Connections:
*sen0: J13.1, J18.1
*sen1: J15.1, J20.1
+5P: J7.1
+15V: J22.1
+iso_5V2: J16.1
A+5V: J9.1
A-5V: J10.1
GND: J6.1
GNDA: J8.1
ISOGND2: J21.1
sen0: J2.1, J12.1, J17.1
sen1: J4.1, J14.1, J19.1
vac_n0: J3.1
vac_n1: J11.1
vac_p0: J1.1
vac_p1: J5.1
