blakhall/Kicad/schematic/main/power.kicad_sch

## KiCad design schematic/main/power.kicad_sch (2026-04-12, an earlier design)

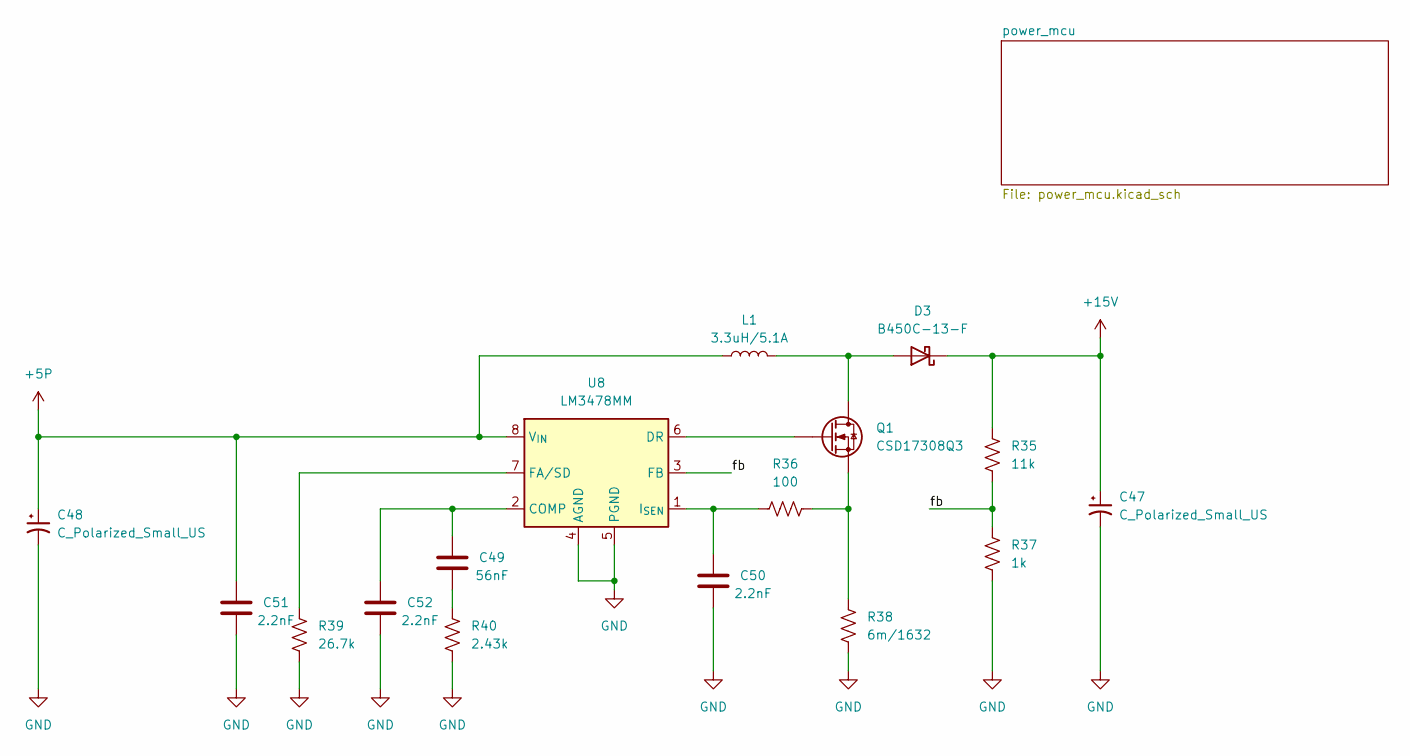
[picture p124: schematic power.kicad_sch]

Parts:
C47, C48: C_Polarized_Small_US
C49: 56nF; C_0603_1608Metric; Part Number any
C50, C51, C52: 2.2nF; C_0603_1608Metric; Part Number any
D3: B450C-13-F; Part Number B450C-13-F
L1: 3.3uH/5.1A; Part Number XAL7070-332MEB
Q1: CSD17308Q3
R35: 11k; R_0603_1608Metric
R36: 100; R_0603_1608Metric
R37: 1k; R_0603_1608Metric
R38: 6m/1632; R_0612_1632Metric; Part Number PRL1632-R006-F-T1
R39: 26.7k; R_0603_1608Metric
R40: 2.43k; R_0603_1608Metric
U8: LM3478MM; VSSOP-8_3x3mm_P0.65mm

Connections:
+5P: C48.1, C51.2, L1.1, U8.8 (V_{IN})
+15V: C47.1, D3.1 (K), R35.1
GND: C47.2, C48.2, C50.1, C51.1, C52.1, R37.2, R38.1, R39.1, R40.1, U8.4 (AGND), U8.5 (PGND)
unnamed: C49.1, R40.2
unnamed: C49.2, C52.2, U8.2 (COMP)
unnamed: C50.2, R36.2, U8.1 (I_{SEN})
unnamed: D3.2 (A), L1.2, Q1.5 (D), Q1.6 (D), Q1.7 (D), Q1.8 (D), Q1.9 (D)
unnamed: Q1.1 (S), Q1.2 (S), Q1.3 (S), R36.1, R38.2
unnamed: Q1.4 (G), U8.6 (DR)
unnamed: R39.2, U8.7 (FA/SD)
fb: R35.2, R37.1, U8.3 (FB)
